gunnarbeutner/doorbell/captures/runs/our-ring-no-door/notes.md

# our-ring-no-door — our ring, session held ~59 s, then released without a door-open

Our front-door ring: line 4 goes hot, the 3-Klang gong rides the front, and a session holds for
**~58.5 s** — then it ends in a **plain release, not a door-open** (P3 never moves, no P2↔P3
bridge). So "no answer" here means **nobody opened the door**: the call was picked up / line 4
latched and held, the gong played out, and the session timed out / was hung up with the opener
never fired. Consistent with the session model from `our-ring-door-open` and `our-ring-after-neighbour`
— but ending at the *handset/timeout* side, not the door-release side.

This capture is at **50 kSa/s** — double the older 25 kSa/s runs — so the onset pedestal-then-tone
sequencing resolves cleanly (20 µs/sample).

## Capture

| | |
|---|---|
| Date | 2026-06-21 13:58:09 |
| Sample rate | **50 kSa/s** (Nyquist 25 kHz; dt = 20 µs — verified from CSV Δt and the 50 kHz WAV header) |
| Duration / points | 100.0 s, 4,999,999 samples/channel |
| Probe ratio | 10× |
| Channels (grounds on **P1**) | **CH1 = IN_P4 (= P4, bridged)**, **CH2 = P2**, **CH3 = P3** — *assumed* from the prior sessions' convention (no pre-existing note for this capture); the data is consistent with it (CH1 carries the latched line-4 pedestal + front gong, CH2 the 12 V listen line, CH3 the quiet high-Z talk line). |
| Files | `*-ch{1,2,3}.csv` / `.wav`, `*.png` |

Times are **elapsed seconds** from the start.

## Timeline

| Elapsed | Event |
|---|---|
| 0 – 31.25 s | Idle. P2 **+12.107 V**, line 4 **−0.02 V**, P3 **−0.01 V** (P3 carries ~0.59 V RMS of broadband high-Z hum, no DC). |
| **~31.250 s** | **Our ring** — line 4 (IN_P4 = P4) goes hot; pedestal rises **0.5 V → 8 V in ~5.9 ms** (1 V at 31250.0 ms, 8 V at 31255.9 ms), brief onset overshoot to ~11.1 V. P2 sags **12.1 → ~9.4 V**. **1010 Hz** gong on line 4 **and** P2. |
| 31.25 – ~35.1 s | **Gong** — 3-Klang on the front: **1010 Hz (+ strong 3030 Hz harmonic) → 840 Hz → 672 Hz**, decaying; audible for **~3.9 s**, then flat DC. |
| 31.25 – 89.79 s | **Session held — ~58.5 s.** Line 4 steady **9.25 V**, P2 **9.43 V** (line 4 sits **0.18 V below P2**, pulled up *from* P2 through the latched contact — the handset seal-in). P3 flat at 0 V the whole time (max DC excursion 0.05 V). No further bursts. |
| **~89.794 s** | **Session released — no door-open.** Line 4 collapses **9.19 → 0 V in ~34 ms**; **P2 falls *with* it** to ~2.66 V (the tied pair dropping together, CH2 staying above CH1 the whole way down), then **P2 snaps back** — 11.5 V by +44 ms, 12.1 V by +112 ms. **P3 never moves** (≤0.05 V DC). |
| 89.9 – 100 s | Idle. P2 +12.11 V, line 4 & P3 ≈ 0 V. |

## Findings

**This is *our* ring, and it was answered — but the door was never opened.** All the *our-door*
markers are present: line 4 itself goes hot (9.25 V, not just a bleed onto P2), the gong is **on
line 4**, and a session seals in and holds. What's **missing** is the door-open. In `our-ring-door-open`
and `our-ring-after-neighbour` the session ends with **P3 jumping 0 → ~7–9 V and a P2↔P3 bridge**; here P3
stays cold (max 0.05 V) and there is **no bridge** — instead the whole tied P2/line-4 pair collapses
together and P2 recovers in ~110 ms. That is a **plain seal-in release** (hang-up / call timeout),
not a door-release transfer. The discriminator is P3: a door-open shows on P3, and **P3 is flat
through the entire 100 s**. → ring answered, opener never fired.

**The end is a release, not a door-open — confirmed on three counts:**
- **P3 never rises.** A door-open is a P2↔P3 short pulling P3 up to ~7 V; here P3's DC never leaves
  the noise floor (≤0.05 V).
- **P2 is *driven* low — the TV20/S pulls P2, not line 4.** The tied pair drops together (CH2 stays
  ~0.18 V above CH1 through the fall), but the tell is *after* separation: **P2 holds a ~2.8 V plateau
  for ~18 ms while line 4 is already down near 0**, then snaps back to 12 V (~112 ms total). A *held*
  low = P2 actively driven — were line 4 the driven node, P2 would recover the instant K5 releases; P2
  also **leads** line 4 at the fall onset by ~60–100 µs. So the latch drops via a **brief P2-low
  pulse** (the K5 coil loses its P2 supply), not a P2↔P3 door-open short (slow ~1.5 s ramp,
  `door-open-standalone`).
- **No bridge meet-point.** P2 and P3 never converge to a common ~7 V level.

**Tone lags the line-4 pedestal — the reactive-suppress window is here too.** At 50 kSa/s the
onset resolves: the line-4 **pedestal** crosses 1 V at **31250.0 ms** and 8 V at **31255.9 ms**;
an **edge transient** rides the step at ~31249–31251 ms, then the AC envelope **falls back to the
noise floor** (~0.06 V) for ~31251–31262 ms before the **gong tone proper ramps in at ~31263–31265
ms** and holds. So the audible chime starts **~13–15 ms after** the pedestal begins — the same
~10–15 ms gap noted in `our-ring-after-neighbour`. Enough to suppress the gong **reactively** (a relay's ~5 ms
pull-in just fits; a PhotoMOS fits easily) — chime-suppress does **not** need pre-arming.

**Gong:** **~1010 Hz** fundamental with a strong **3030 Hz** 3rd harmonic at onset, descending
through **~840 Hz** to **~672 Hz** (the 3-Klang, a falling sequence), decaying over ~3.9 s — matches
the 1010 / 3032 / 672 Hz chime of `our-ring-door-open` and `neighbour-ring-door-open`.

Fitted additive model (heterodyne envelope tracking + Theil–Sen exponential fit on the
bandpassed/denoised CH1 audio; onset amplitudes in dB re the strike-1 peak-normalised extract):
the fundamentals sit at **6:5:4 over the 672 Hz root — a descending major triad** (fifth, third,
root), and each strike is an **odd-harmonic series** (1f, 3f, 5f, 7f…) — the signature of the
TV20/S tone generator, not a struck bell.

| Strike (onset) | Partials — f (Hz) / onset dB / τ (ms) |
|---|---|
| 1 (0 ms) | 1010.2 / −5.8 / 1353 · 3030.7 / −17.9 / 1361 · 5051.1 / −27.8 / 1439 |
| 2 (790 ms) | 840.5 / −9.2 / 1135 · 2521.6 / −21.3 / 1332 · 4202.7 / −29.2 / 1468 · 5883.8 / −38.8 / 1740 · 1849.2 / −42.5 / 4093 |
| 3 (1552 ms) | 672.4 / −10.8 / 1502 · 2017.2 / −20.8 / 1480 · 3362.0 / −27.3 / 1414 · 4706.8 / −33.6 / 1452 · 6051.6 / −40.9 / 1889 |

The 1010 Hz fundamental beats (a close doublet — its envelope has periodic nulls), so short-window
decay fits fail on it; the τ values above come from full-ring-out tracking with noise-floor
truncation. `firmware/sounds/candidates/gong-remaster.wav` is a noise-free additive resynthesis
from this table.

**Session geometry matches the handset seal-in model.** Line 4 holds at **9.25 V**, **0.18 V below
P2 (9.43 V)** — line 4 is pulled up *from* P2 through the latched contact, not driven by the
TV20/S, so it tracks just under P2 (the same 0.1–0.2 V offset as the other held sessions). P2's
~2.67 V sag (12.11 → 9.43 V) is the latched coil loading the shared line. The session simply runs
its course (~58.5 s) and releases — no door in the loop.

## Notes

- **IN_P4↔P4 bonded** for this run, so CH1 is line 4 itself (WF26 coil + C1 in the loop); a
  "line 4 hot" reading is unambiguously *our* door.
- **P3 (CH3) idles as a high-Z antenna** — ~0.59 V RMS, ~4.7 Vpp, **broadband (strongest 0.6–3.5
  kHz), DC-free** — same high-impedance-node signature as IN_P4 in `neighbour-ring-door-open`. It
  carries no DC at any point, which is exactly why "P3 never moves" is a clean no-door-open test.
- The ~58.5 s hold is much longer than the ~10–13 s sessions that ended in a door-open
  (`our-ring-door-open`, `our-ring-after-neighbour`) — consistent with a call left to time out / hang up rather than
  cut short by the opener.

Related: `our-ring-door-open` (own ring + door-open, the clean session model),
`our-ring-after-neighbour` (own ring + door-open, with a neighbour ring first),
`door-open-standalone` (standalone ÖT — what a real door-open looks like on the bus, absent
here). Bus model: `../DESIGN.md` ("Bell signals", "Door opener", "WF26 internal circuit").
