gunnarbeutner/doorbell/captures/runs/door-open-standalone/notes.md

# door-open-standalone — our own door-opener, triggered standalone

A scope capture of **our** door-opener (ÖT) fired on its own, with **no ring/call active**, to see
the trigger waveform on the bus in isolation. Grabbed with `capture.py --screen` (the displayed
ROLL window, full sample density) — see the scope screenshot `door-open-standalone.jpeg`.

## Capture

| | |
|---|---|
| Date | 2026-06-17 16:57:05 |
| Mode | `--screen` (on-screen window, ROLL) |
| Sample rate | 25 kSa/s |
| Duration / points | 8.00 s, 200,000 samples/channel |
| Probe ratio | 10× |
| Channels (grounds on **P1**) | **CH1 = IN_P4**, **CH2 = P2**, **CH3 = P3** |
| Files | `*-ch{1,2,3}.csv` / `.wav`, `*.png` (DC+AC overview), `door-open-standalone.jpeg` (scope screen) |

Times are **elapsed seconds** from the start (scope axis runs −8.0…0.0 s, trigger at −3 s = 5.0 s
elapsed).

## Timeline

| Elapsed | Event |
|---|---|
| 0 – 1.75 s | Idle. P2 +12.06 V, P3 +0.04 V, IN_P4 ≈ 0 V. |
| **~1.75 s** | **Door-opener engages** — P2↔P3 short. P2 drops fast (12 → ~7 V), P3 snaps up (0 → ~7 V). |
| 2.0 – 3.4 s | **Bridged: both held at ~7.16 V** (P2 7.14, P3 7.18 — essentially equal) for ~1.5 s. |
| **~3.5 s** | **Released** — P3 snaps back to 0 V quickly; **P2 recovers slowly**, ramping 7 → 12 V over ~1.5 s (τ ≈ 0.5 s, with a stall near 10 V). |
| 5.25 – 8 s | Idle again. |

## What it shows / confirms

- **Pure P2↔P3 operation — line 4 untouched.** IN_P4 stays flat at ~0 V (±0.4 V noise floor) the
  whole time, with **no coupling even at the switching edges**. The door-opener is exactly the
  TV20/S test *"Klemmen 2 u. 3 brücken,"* nothing on line 4 — validating **K2 = a direct P2↔P3
  short**.
- **It's a dead short, not a resistive bridge.** P2 and P3 are forced to the *same* level
  (7.14 vs 7.18 V). A 2.2 kΩ bridge (the talk handshake) would leave them *separated*; equal means
  a true short. So the door path is cleanly distinguished from the talk path — the practical side of
  the "short fires the opener, 2.2 kΩ doesn't" threshold.
- **The meet point (~7.16 V) is impedance-divided, not midpoint.** From 12 V and 0 V landing at
  7.16 V ⇒ P2's source is ~1.5× stiffer than P3's pull-to-0 (R3/R2 ≈ 1.5).
- **Asymmetric recovery (new):** the short yanks P2 *down* fast (low-Z), but P2 climbs *back* slowly
  (~1.5 s, τ ≈ 0.5 s) through its own bias-source resistance into the bus capacitance. So **after a
  door-open, line 2 takes ~1.5 s to settle back to 12 V** — the codec's RX tap would see a slow DC
  drift upward for ~1.5 s following any door-open (relevant to RX timing / AGC).
- **No audio.** Standalone open (no ring) ⇒ pure DC bridge + switching transients at the make/break
  edges; nothing tonal.

## Caveat

This is the **trigger waveform** as seen on our bus, **not** the opener *firing*. The actual
8–12 V AC solenoid current is switched at the TV20/S / door end, off our tap — to confirm the door
physically released you'd need to hear/see it (or scope the opener pair).

Related: `neighbour-ring-door-open` (neighbour ring with a door-open mid-call),
`neighbour-ring-5ksps`, `idle-20260617-143740`. Bus model: `../DESIGN.md` ("Door opener",
"WF26 internal circuit").
