gunnarbeutner/doorbell/docs/design/HJR4102.PDF

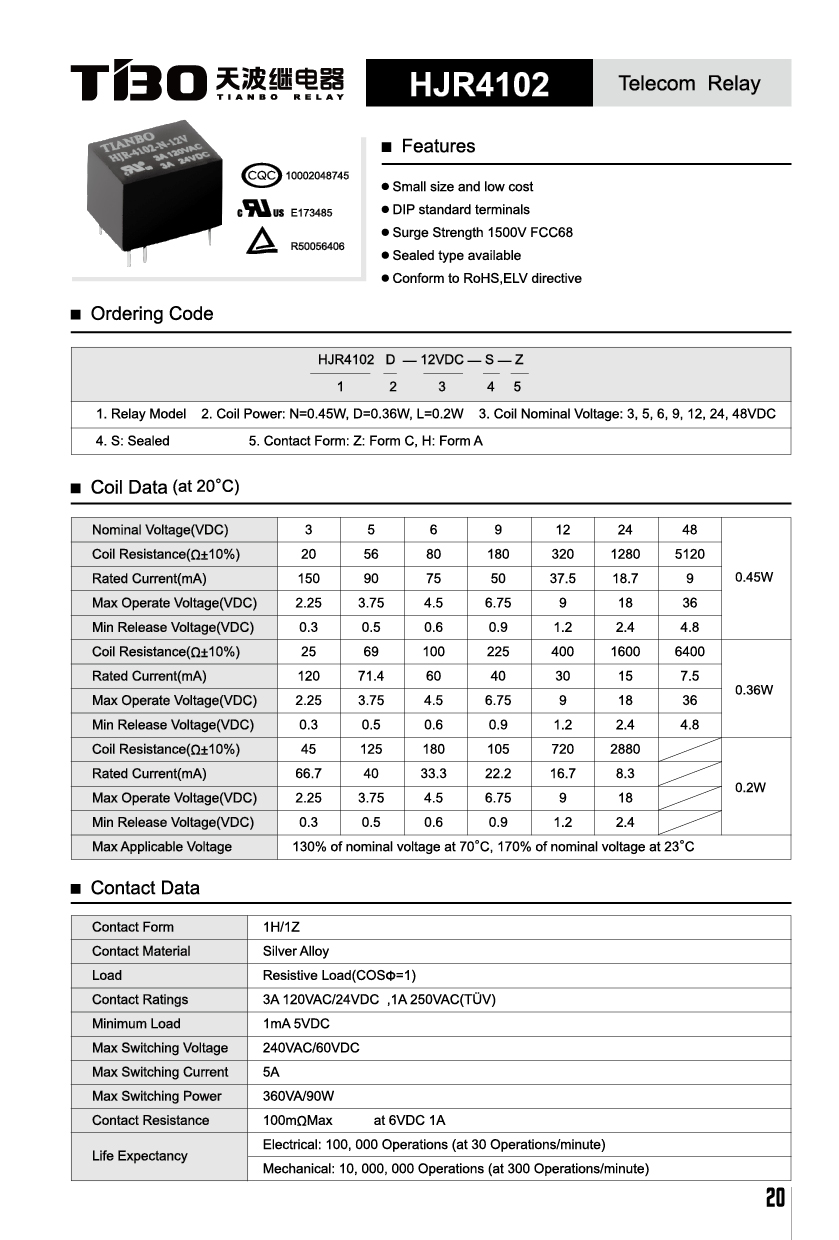
[picture p2: page 1]
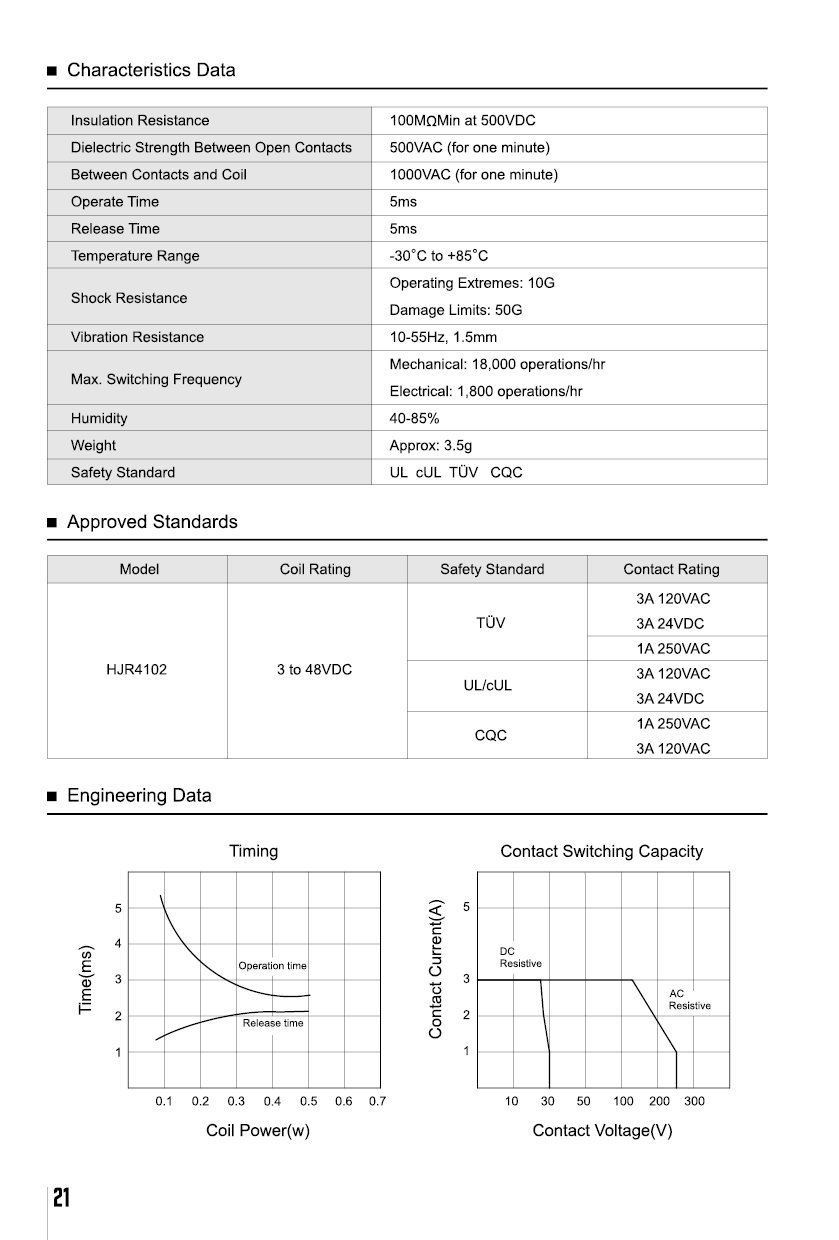
[picture p3: page 2]
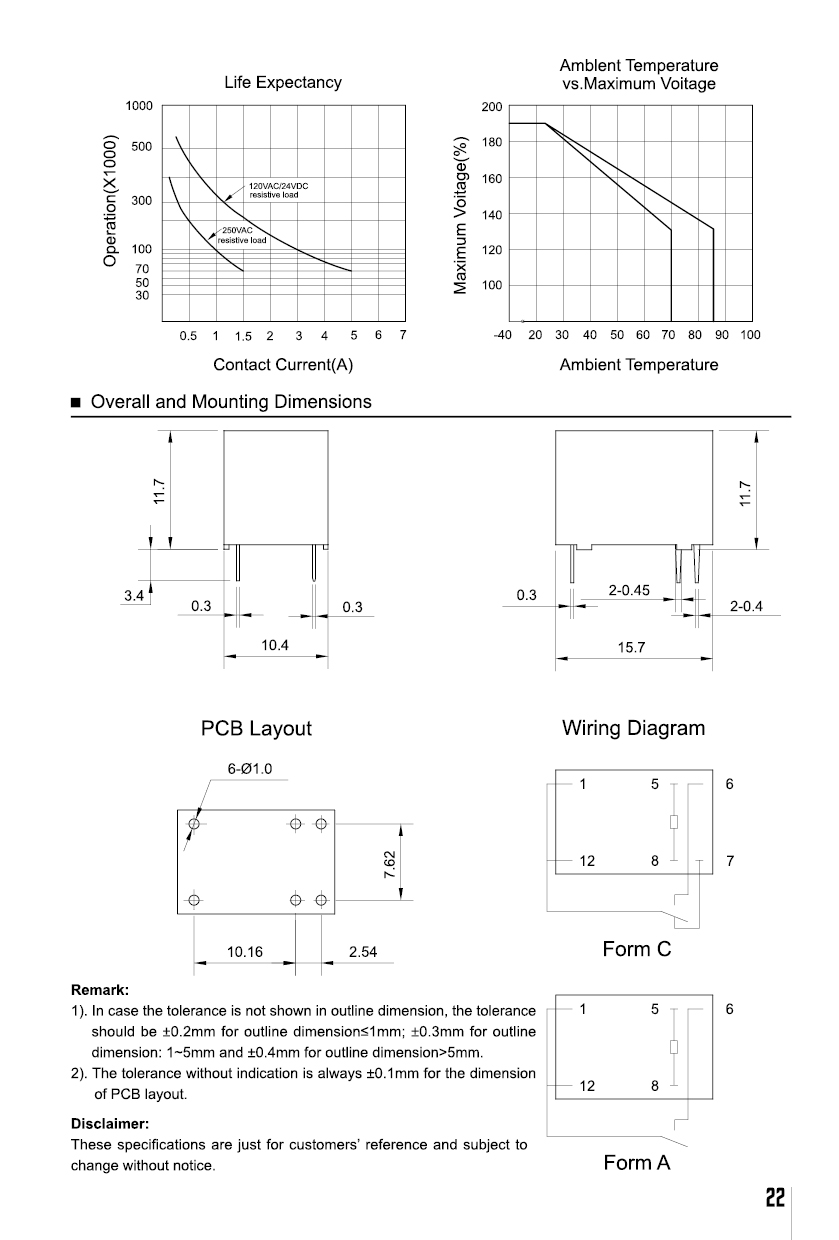
[picture p4: page 3]
