gunnarbeutner/doorbell/captures/runs/door-open-call-held/preview.png

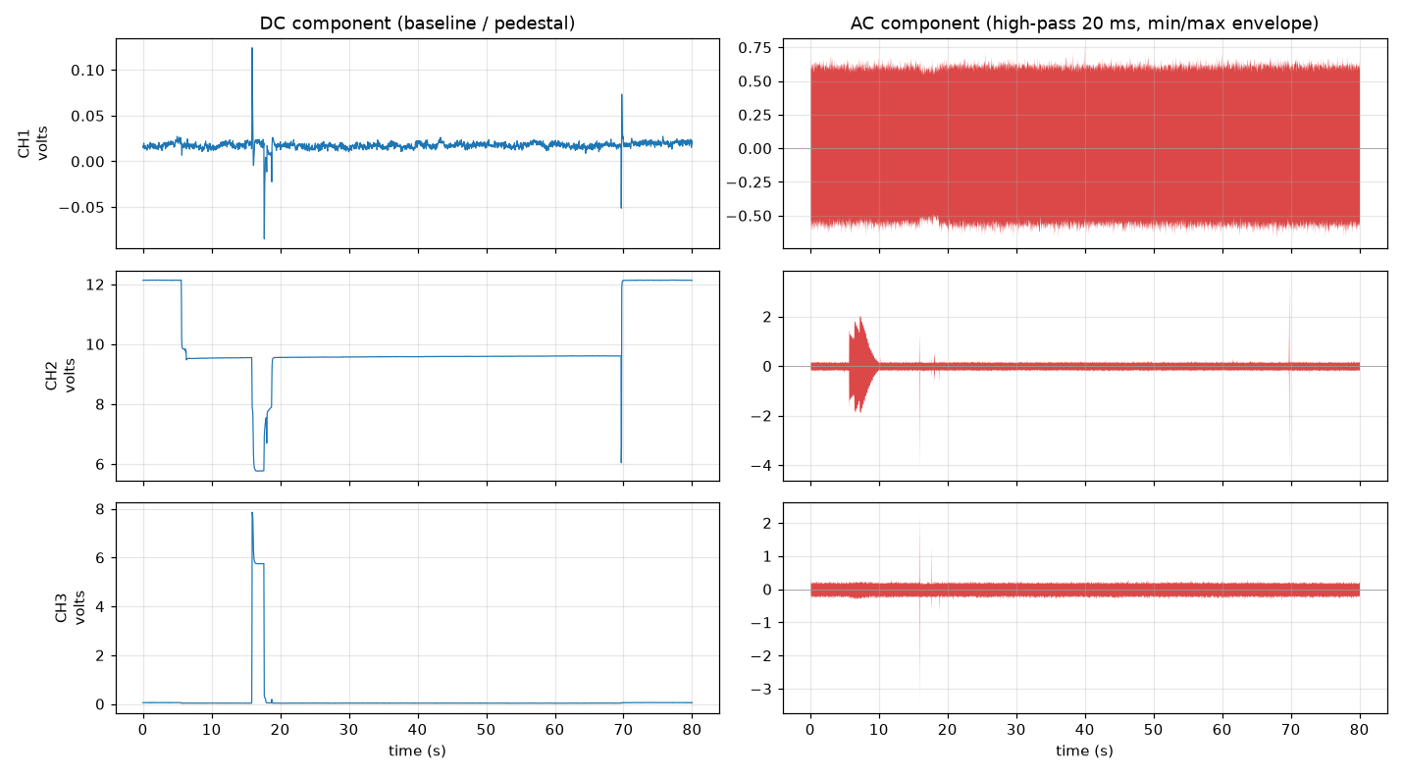
captures/runs/door-open-call-held/preview.png
