gunnarbeutner/doorbell/captures/runs/door-open-standalone/preview.jpeg

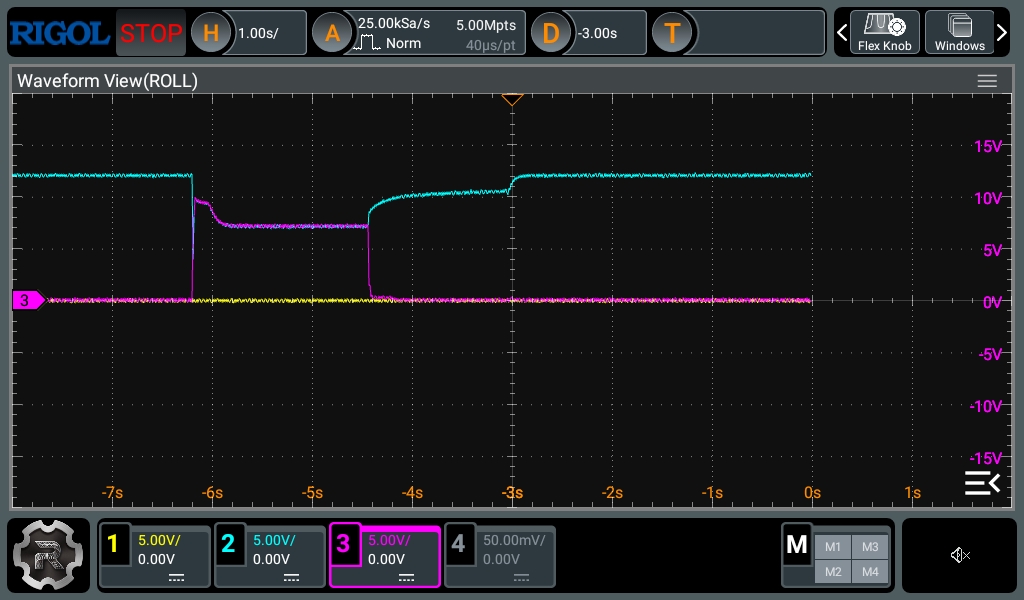
captures/runs/door-open-standalone/preview.jpeg
