gunnarbeutner/doorbell/captures/runs/door-open-standalone/preview.png

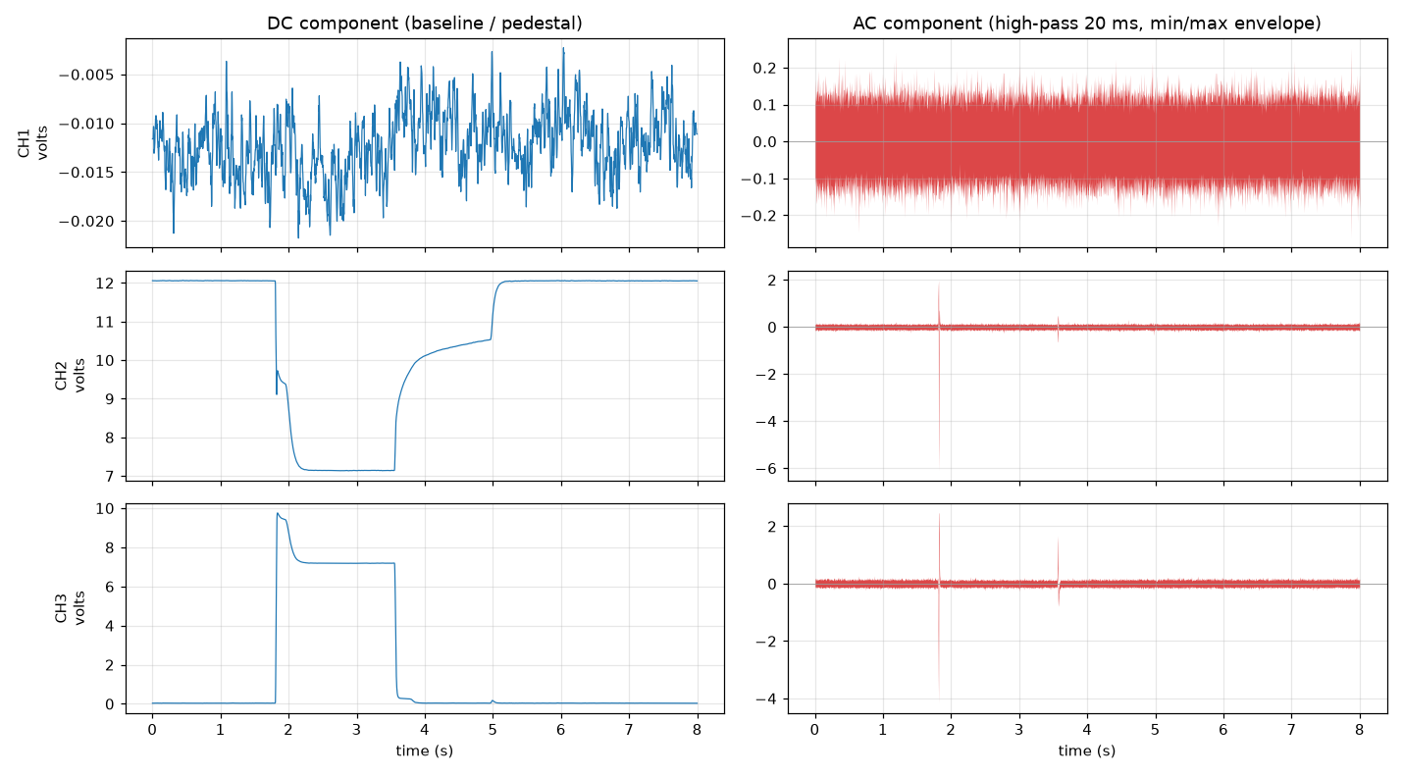
captures/runs/door-open-standalone/preview.png
