gunnarbeutner/doorbell/captures/runs/floor-call-p5/preview.png

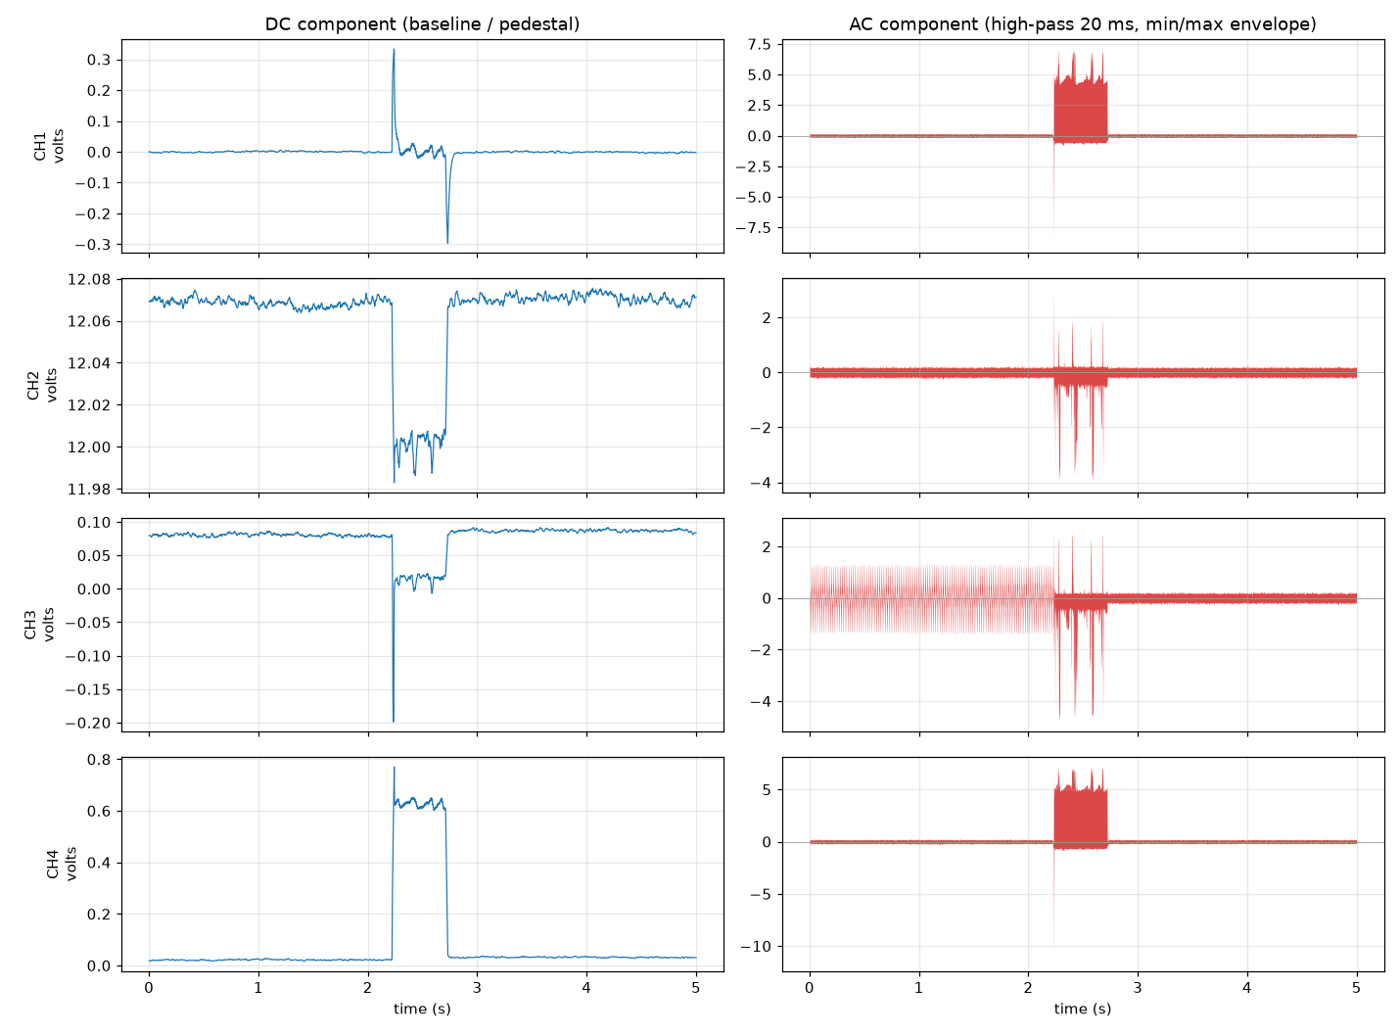
captures/runs/floor-call-p5/preview.png
