gunnarbeutner/doorbell/captures/runs/neighbour-ring-5ksps/preview.png

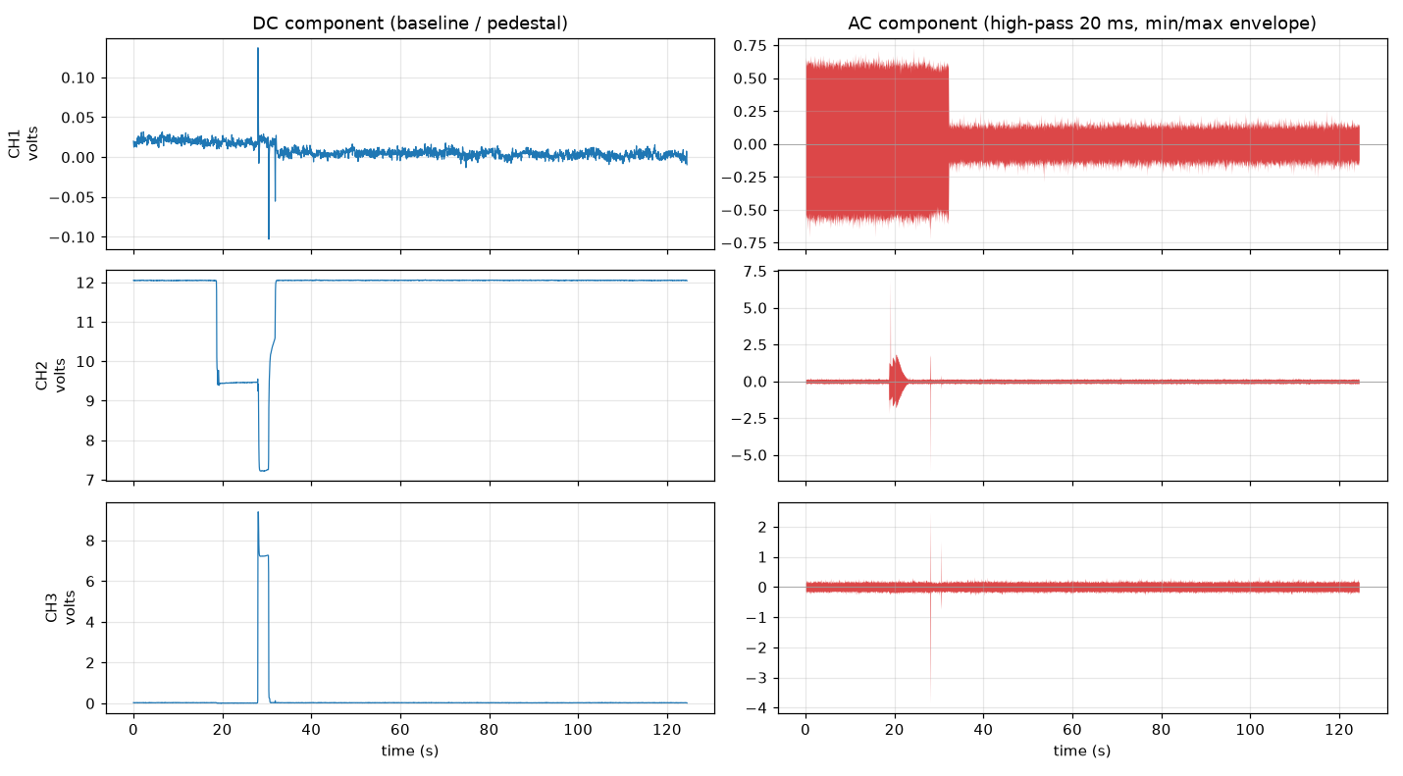
captures/runs/neighbour-ring-5ksps/preview.png
