gunnarbeutner/doorbell/captures/runs/neighbour-ring-door-open/preview.png

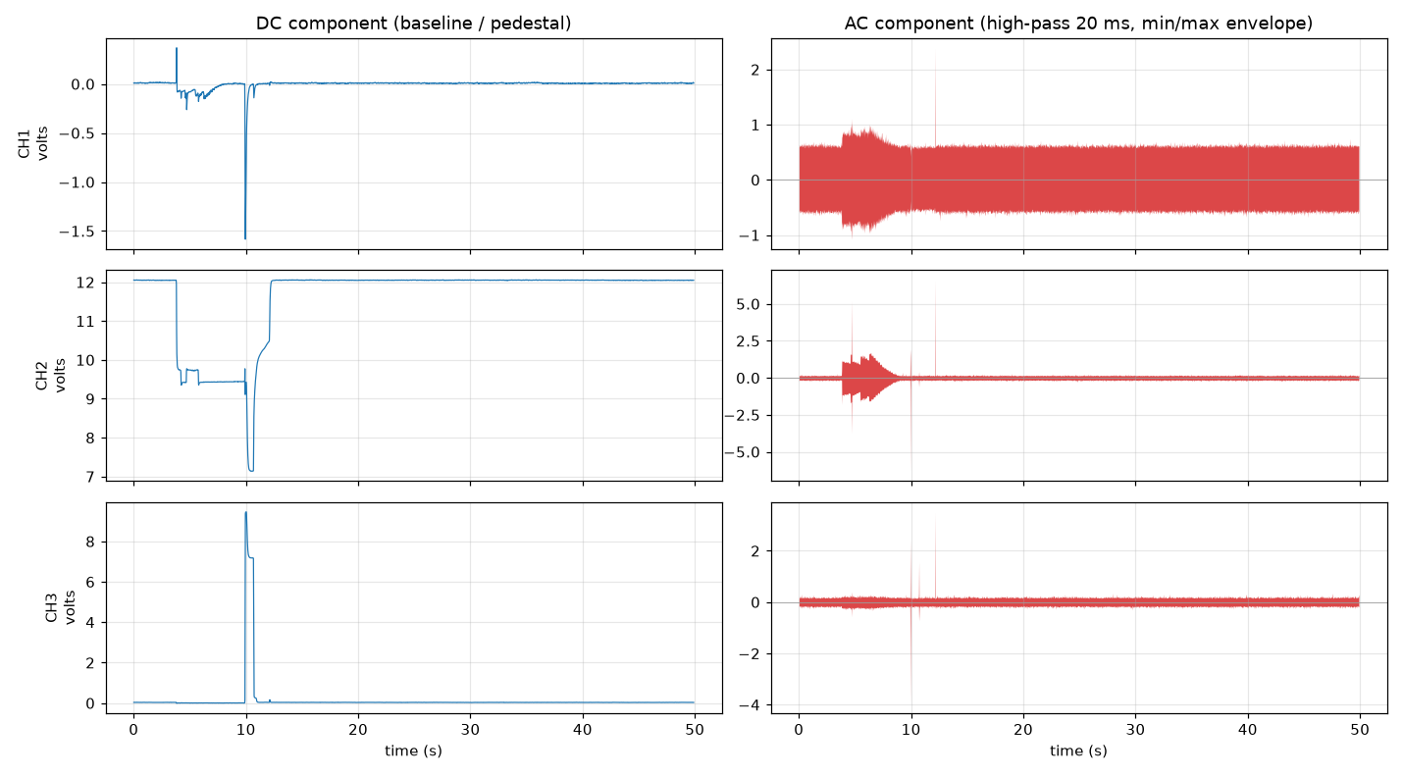
captures/runs/neighbour-ring-door-open/preview.png
