gunnarbeutner/doorbell/captures/runs/our-ring-after-neighbour/preview.png

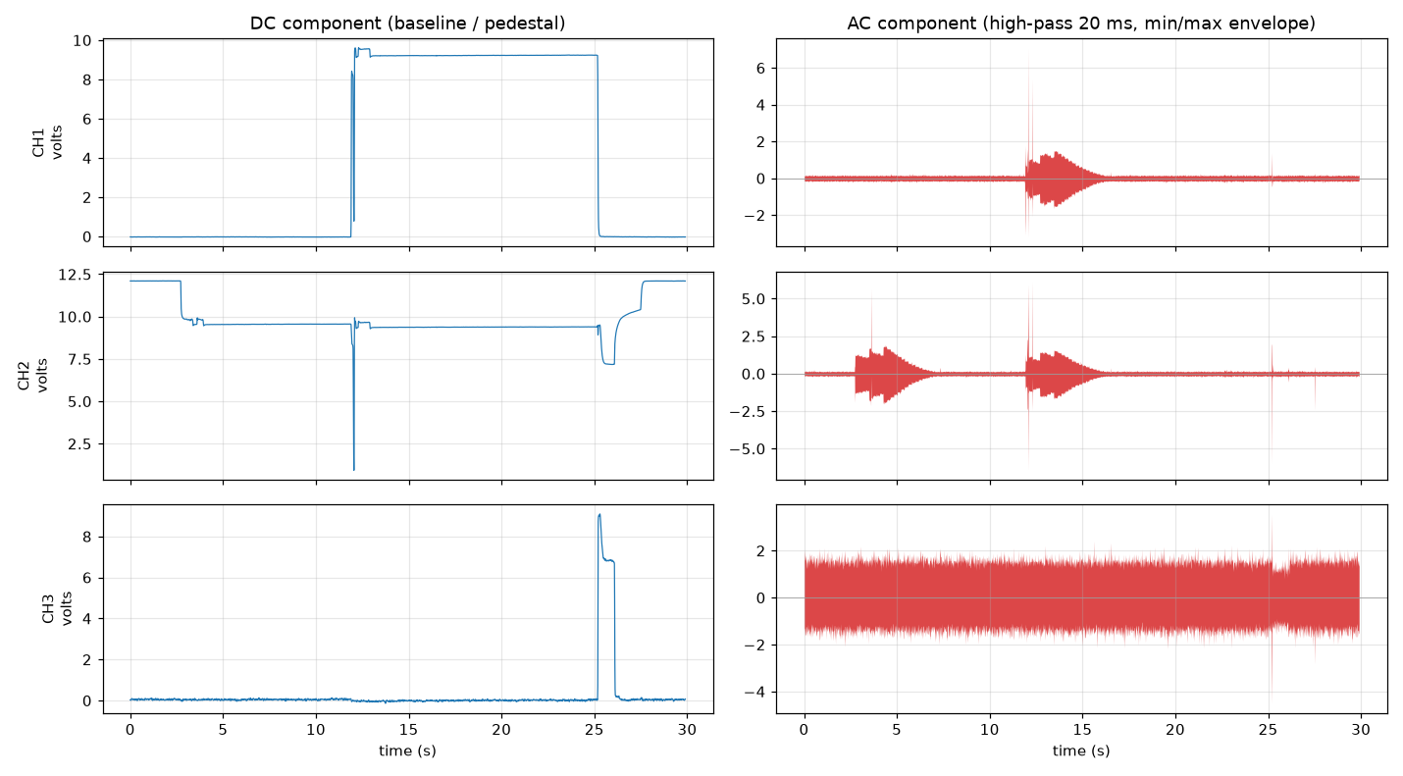
captures/runs/our-ring-after-neighbour/preview.png
