gunnarbeutner/doorbell/captures/runs/our-ring-door-open/preview.png

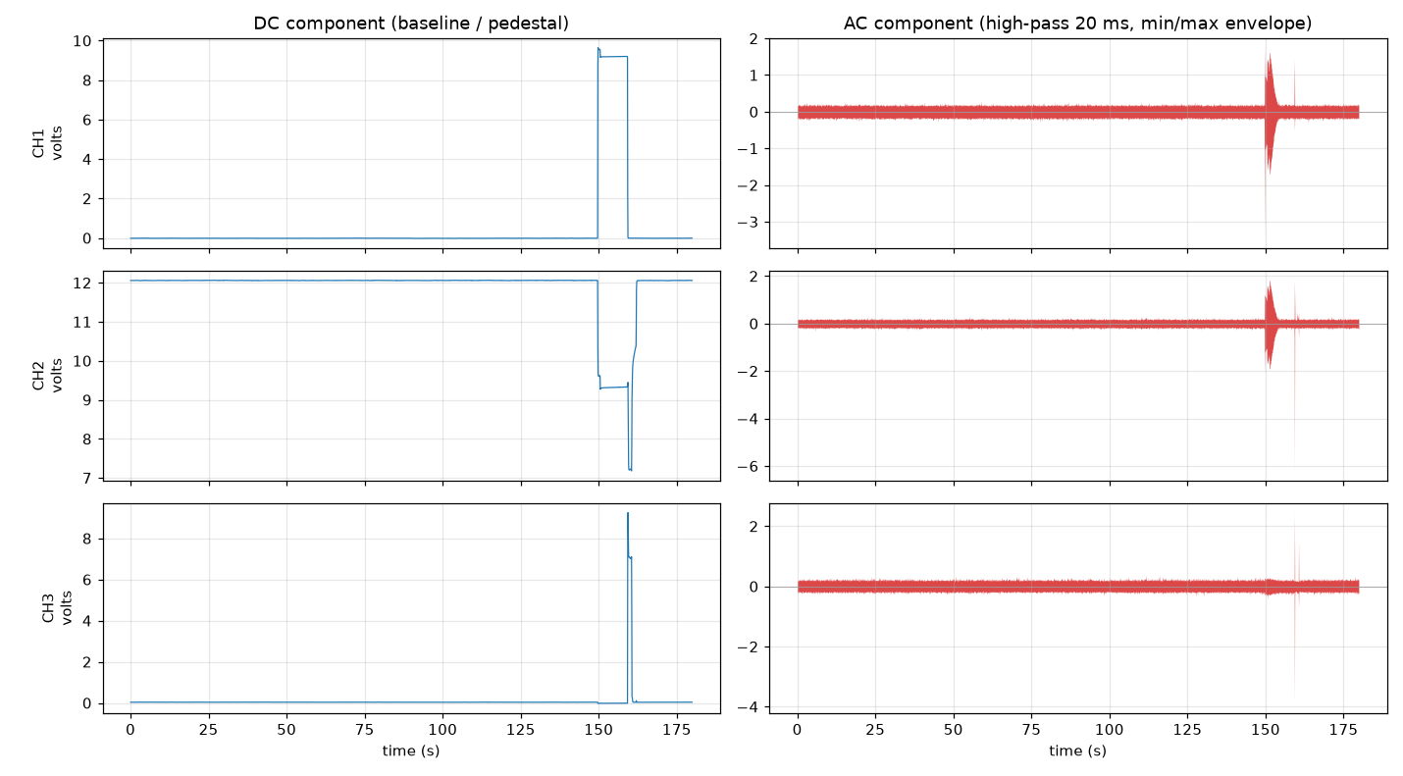
captures/runs/our-ring-door-open/preview.png
