gunnarbeutner/doorbell/captures/runs/our-ring-no-door/preview.png

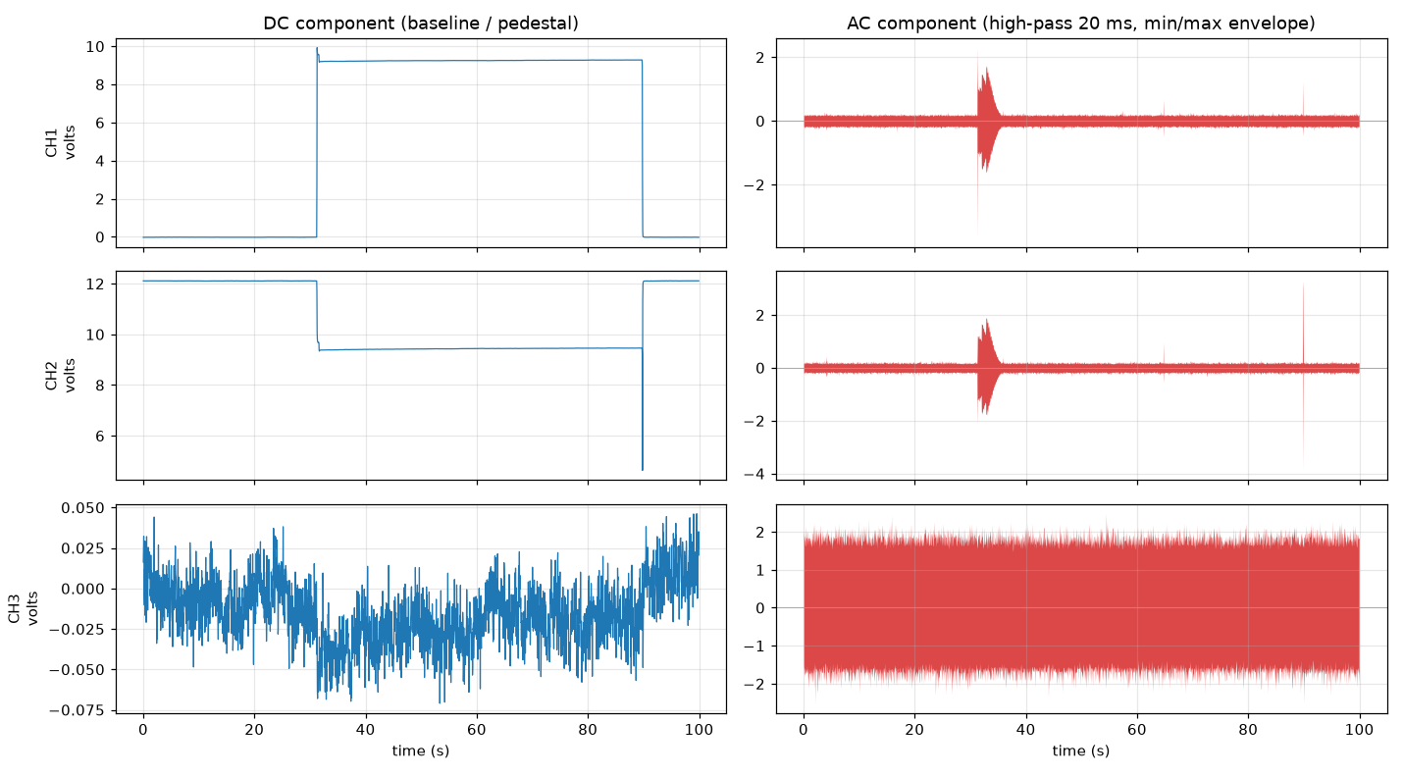
captures/runs/our-ring-no-door/preview.png
