gunnarbeutner/doorbell/captures/runs/our-ring-p4-floating/p1-p4-ring.png

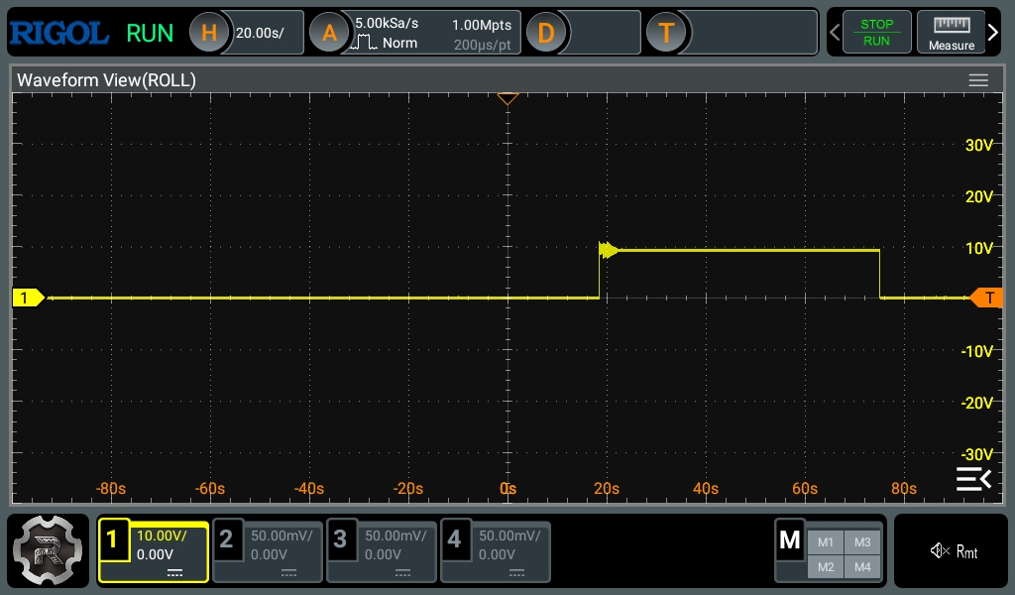
captures/runs/our-ring-p4-floating/p1-p4-ring.png
