gunnarbeutner/doorbell/captures/runs/our-ring-p4-floating/preview.png

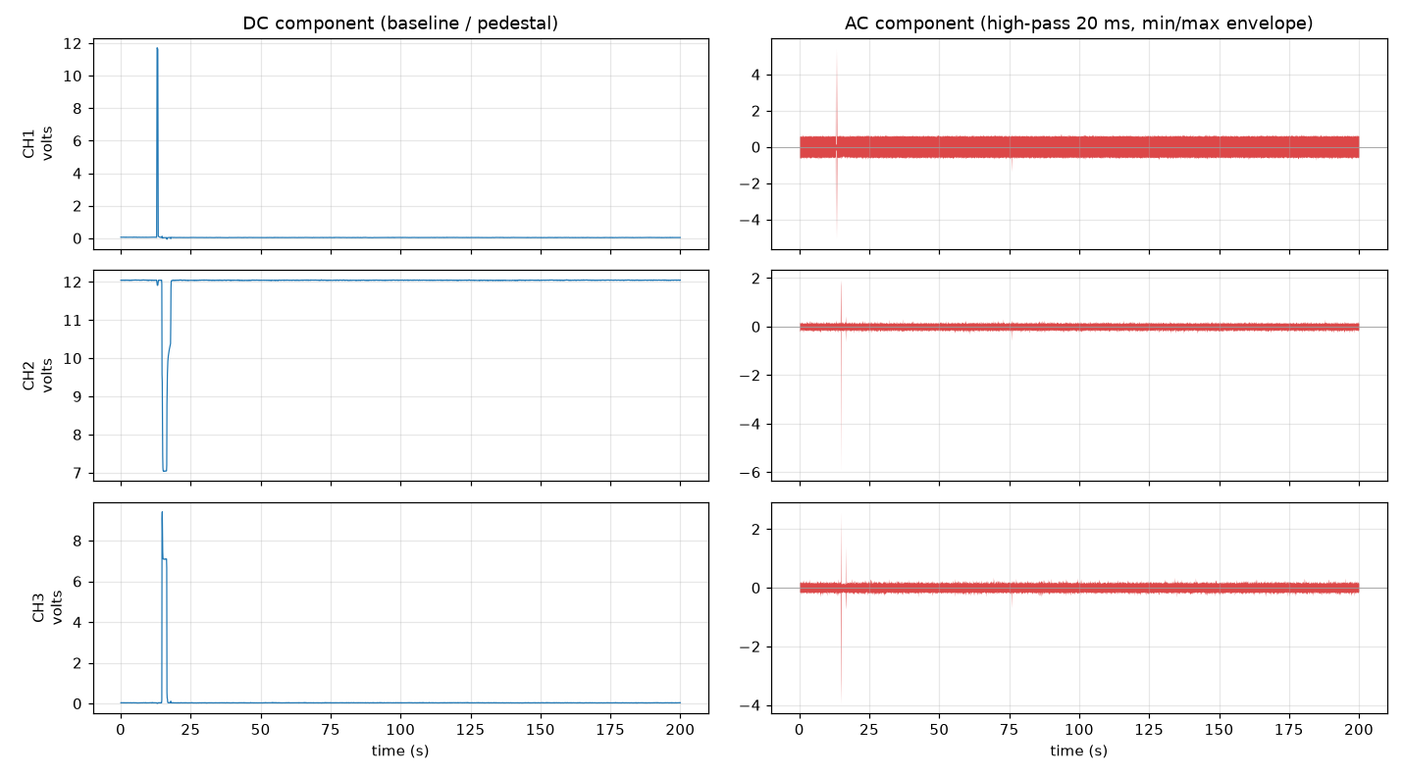
captures/runs/our-ring-p4-floating/preview.png
