gunnarbeutner/doorbell/docs/scope/k3-usb-power-loss.png

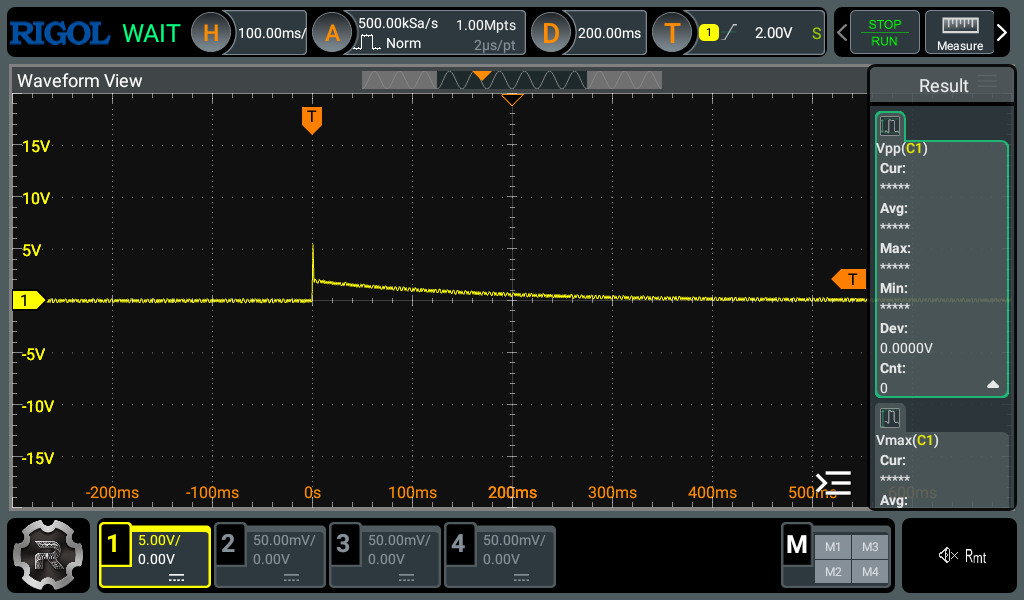
docs/scope/k3-usb-power-loss.png
