gunnarbeutner/doorbell/docs/scope/welcome-chime-p3.png

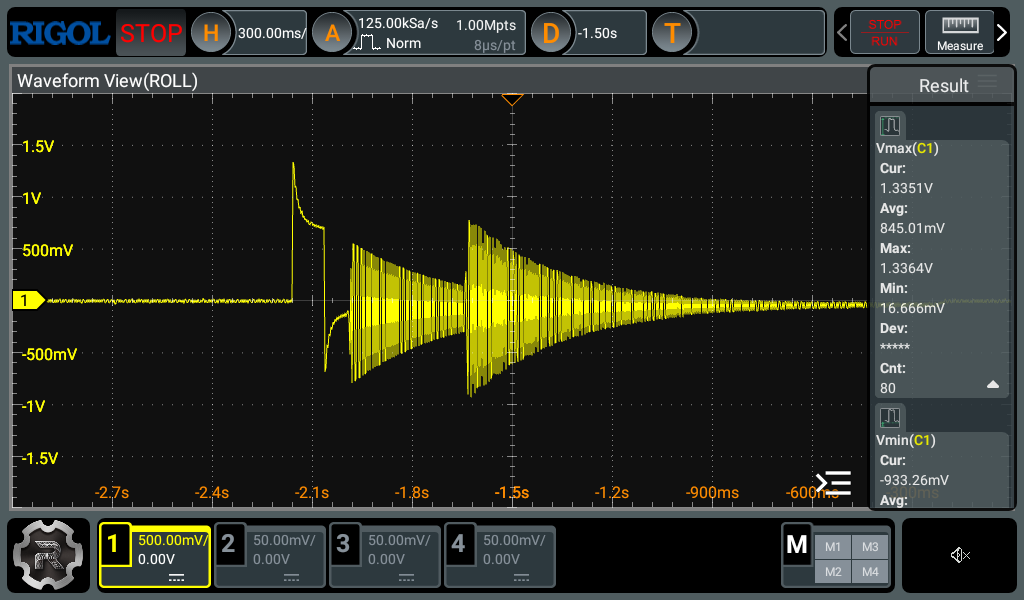
docs/scope/welcome-chime-p3.png
