gunnarbeutner/doorbell/docs/scope/door-break-before-make.png

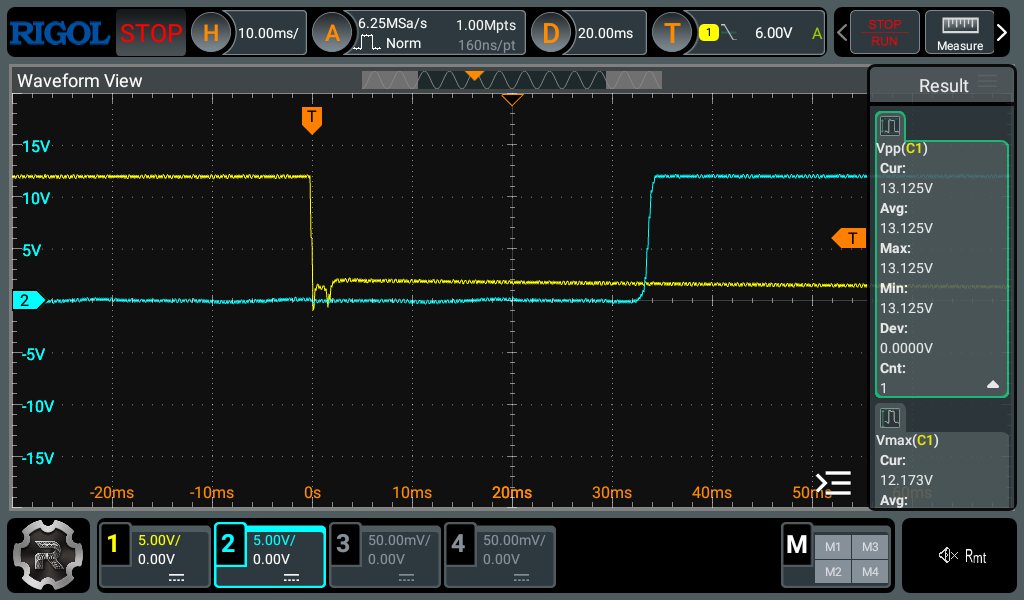
docs/scope/door-break-before-make.png
