gunnarbeutner/doorbell/sim/firmware-test/circuit-runner.js

import { EventEmitter } from 'node:events';
import net from 'node:net';

import { importNetlist } from '../src/import.js';
import { buildElements, defaultSwitchState } from '../src/components/index.js';
import { createStepper, gndOf, makeWave } from '../src/engine.js';
import { Tv20sEnvironment } from '../src/tv20s/environment.js';

export const PROTOCOL_VERSION = 1;

const GPIO_TO_SIGNAL = Object.freeze({
  4: 'K5_SENSE_N',
  5: 'VBUS_F_ADC',
  9: 'PTT_DRV',
  10: 'DOOR_DRV',
  11: 'MUTE_DRV',
  12: 'P4_SENSE_N',
  13: 'P5_SENSE_N',
  47: 'PTT_SENSE_N',
  48: 'P4_ISO',
});

const EXPECTED_U1 = Object.freeze({
  4: '/K5_SENSE_N',
  5: '/VBUS_F_ADC',
  17: '/PTT_DRV',
  18: '/DOOR_DRV',
  19: '/MUTE_DRV',
  20: '/P4_SENSE_N',
  21: '/P5_SENSE_N',
  24: '/PTT_SENSE_N',
  25: '/P4_ISO',
});

const IMPORTANT_NETS = ['/P2', '/P3', '/P4', '/P5', '/K5_LATCH', '/K6_RET', '/CHIME_POS'];

let cachedHeadNetlist;
let cachedReferenceNetlist;
const cachedDefaultStates = new Map();

function liveHeadNetlist() {
  // Every suite invocation imports HEAD from KiCad. Reusing the immutable result within that
  // invocation avoids launching kicad-cli once per fresh firmware scenario.
  cachedHeadNetlist ??= importNetlist();
  return cachedHeadNetlist;
}

function liveReferenceNetlist() {
  cachedReferenceNetlist ??= importNetlist('wf26');
  return cachedReferenceNetlist;
}

function source(value = 0) {
  if (value === null) return { kind: 'off', value: 0, offset: 0, amplitude: 0, frequency: 0 };
  return { kind: 'dc', value, offset: 0, amplitude: 0, frequency: 0 };
}

export class HeadCircuitFixture {
  constructor({ startMs = 0, timeline = [], netlist, onSample = null, environment = 'lab',
    referenceNetlist } = {}) {
    this.netlist = netlist || liveHeadNetlist();
    this.validateHeadMapping();
    this.timeline = timeline;
    this.startMs = Number(startMs);
    this.nowMs = Number(startMs);
    this.electricalMs = Number(startMs);
    this.electricalSeconds = 0;
    this.fineUntilMs = this.nowMs;
    this.mediumUntilMs = this.nowMs;
    this.externalToneActive = false;
    this.outputs = { PTT_DRV: false, DOOR_DRV: false, MUTE_DRV: false, P4_ISO: false };
    this.mediaActive = false;
    this.sources = {
      P2: source(12),
      P4: source(null),
      P5: source(null),
      VBUS: source(5),
    };
    this.switches = { ...defaultSwitchState(this.netlist), SW3: false, SW4: false };
    this.programPresent = true;
    this.lastInputMask = null;
    this.indeterminateSince = {};
    this.lastElectrical = {};
    this.onSample = onSample;
    if (!['lab', 'tv20s'].includes(environment)) throw new Error(`unknown circuit environment ${environment}`);
    this.environmentMode = environment;
    this.tv20s = environment === 'tv20s' ? new Tv20sEnvironment({
      startMs, calibration: undefined, referenceNetlist: referenceNetlist || liveReferenceNetlist(),
      ground: gndOf(this.netlist),
    }) : null;
    this.interactiveSources = null;
    this.interactiveExtra = [];
    this.dcOperatingPoint = null;
    const cacheKey = `${environment}:${this.netlist.source}`;
    const cachedDefaultState = cachedDefaultStates.get(cacheKey);
    this.rebuild(0.0002, cachedDefaultState);
    if (cachedDefaultState === undefined) {
      // Fixture initialization represents a board whose standing rails have already reached their
      // DC operating point. Solve that point directly; do not confuse an arbitrary transient duration
      // with electrical settling. Every scenario receives its own copy of this immutable seed.
      const settled = this.stepper.operatingPoint(this.electricalSeconds).state;
      cachedDefaultStates.set(cacheKey, settled);
      this.rebuild(0.0002, settled);
    }
    this.fineUntilMs = this.nowMs;
    this.mediumUntilMs = this.nowMs;
    this.timeline.length = 0;
    this.lastElectrical = {};
    this.recordElectrical(true);
    this.lastInputMask = this.readInputs().mask;
    this.recordSample();
  }

  validateHeadMapping() {
    const u1 = this.netlist.components.find((component) => component.ref === 'U1');
    if (!u1) throw new Error('HEAD mapping: U1 is missing');
    for (const [pin, expected] of Object.entries(EXPECTED_U1)) {
      if (u1.pins[pin] !== expected)
        throw new Error(`HEAD mapping: U1 pin ${pin} must be ${expected}, got ${u1.pins[pin] ?? '(missing)'}`);
    }
    const j2 = this.netlist.components.find((component) => component.ref === 'J2');
    const expectedBus = { 1: 'GND', 2: '/P2', 3: '/P3', 4: '/P4', 5: '/P5' };
    for (const [pin, expected] of Object.entries(expectedBus))
      if (j2?.pins[pin] !== expected)
        throw new Error(`HEAD mapping: J2.${pin} must be ${expected}, got ${j2?.pins[pin] ?? '(missing)'}`);
  }

  validateHello(tokens) {
    const advertised = Object.fromEntries(tokens.map((token) => token.split('=')));
    for (const [pin, signal] of Object.entries(GPIO_TO_SIGNAL)) {
      if (advertised[signal] !== pin)
        throw new Error(`HELLO mapping mismatch for ${signal}: expected GPIO${pin}, got ${advertised[signal] ?? 'missing'}`);
    }
  }

  valueAt(name) {
    const spec = this.sources[name];
    if (spec.kind === 'tone')
      return spec.offset + spec.amplitude * Math.sin(2 * Math.PI * spec.frequency * this.electricalSeconds);
    if (spec.kind === 'pulse') {
      const elapsedMs = (this.electricalSeconds - spec.startedSeconds) * 1000;
      if (elapsedMs < spec.delayMs) return spec.low;
      const activeMs = elapsedMs - spec.delayMs;
      if (spec.count !== null && activeMs >= spec.count * spec.periodMs) return spec.low;
      return activeMs % spec.periodMs < spec.widthMs ? spec.high : spec.low;
    }
    if (spec.kind === 'captured') {
      const elapsedMs = Math.max(0, (this.electricalSeconds - spec.startedSeconds) * 1000);
      const last = spec.values.length - 1;
      const position = Math.min(last, elapsedMs / spec.dtMs);
      const index = Math.floor(position);
      const fraction = position - index;
      return spec.values[index] + fraction * ((spec.values[index + 1] ?? spec.values[index]) - spec.values[index]);
    }
    return spec.value;
  }

  refreshExternalWave() {
    const waves = Object.values(this.sources).filter((item) =>
      item.kind === 'tone' || item.kind === 'pulse' || item.kind === 'captured');
    this.externalToneActive = waves.length !== 0;
    this.externalStepSeconds = Math.min(0.00025, ...waves.map((item) => {
      if (item.kind === 'captured') return item.dtMs / 1000;
      if (item.kind === 'pulse')
        return Math.max(0.00002, Math.min(item.widthMs, item.periodMs - item.widthMs) / 4000);
      return 1 / (item.frequency * 6);
    }));
  }

  program() {
    if (!this.programPresent) return {};
    return {
      U1: {
        '/PTT_DRV': () => (this.outputs.PTT_DRV ? 3.3 : 0),
        '/DOOR_DRV': () => (this.outputs.DOOR_DRV ? 3.3 : 0),
        '/MUTE_DRV': () => (this.outputs.MUTE_DRV ? 3.3 : 0),
        '/P4_ISO': () => (this.outputs.P4_ISO ? 3.3 : 0),
      },
      U3: {
        out: {
          // A bounded, non-harmonic-to-the-1 ms-step codec representative. It is not a TV20/S
          // acoustic model; it only exercises the board's TX coupling while firmware owns media.
          p: () => 1.65 + (this.mediaActive ? 0.35 * Math.sin(2 * Math.PI * 333 * this.electricalSeconds) : 0),
          n: () => 1.65,
        },
      },
    };
  }

  rebuild(dt, seed = this.stepper?.extractState()) {
    this.dt = dt;
    if (this.tv20s) {
      this.tv20s.syncTime(this.electricalMs);
      const elements = buildElements(this.netlist, {
        switchState: this.switches,
        program: this.program(),
        extra: this.tv20s.extraElements(),
      });
      const sources = [
        { net: '/VBUS', vf: () => this.valueAt('VBUS') },
        ...this.tv20s.sources(),
      ];
      this.stepper = createStepper(elements, sources, gndOf(this.netlist), dt, seed);
      return;
    }
    if (this.interactiveSources !== null) {
      const extra = [...this.interactiveExtra];
      const sources = [];
      for (let index = 0; index < this.interactiveSources.length; index++) {
        const item = this.interactiveSources[index];
        if (item.off) continue;
        const wave = makeWave(item);
        const impedance = Number(item.impedance || 0);
        if (impedance > 0) {
          const sourceNet = `/INTERACTIVE_SOURCE_${index}`;
          extra.push({ type: 'R', a: sourceNet, b: item.net, value: impedance,
            ref: `INTERACTIVE_SOURCE_R${index}` });
          sources.push({ net: sourceNet, vf: () => wave(this.electricalSeconds) });
        } else {
          sources.push({ net: item.net, vf: () => wave(this.electricalSeconds) });
        }
      }
      const elements = buildElements(this.netlist, {
        switchState: this.switches,
        program: this.program(),
        extra,
      });
      this.stepper = createStepper(elements, sources, gndOf(this.netlist), dt, seed);
      return;
    }
    const connectedBusSources = ['P2', 'P4', 'P5'].filter((name) => this.sources[name].kind !== 'off');
    const extra = connectedBusSources.map((name) => ({
      type: 'R',
      a: `/TEST_${name}_SOURCE`,
      b: `/${name}`,
      value: 90,
      ref: `TEST_${name}_SOURCE_R`,
    }));
    const elements = buildElements(this.netlist, {
      switchState: this.switches,
      program: this.program(),
      extra,
    });
    const sources = [{ net: '/VBUS', vf: () => this.valueAt('VBUS') },
      ...connectedBusSources.map((name) => ({ net: `/TEST_${name}_SOURCE`, vf: () => this.valueAt(name) }))];
    this.stepper = createStepper(elements, sources, gndOf(this.netlist), dt, seed);
  }

  invalidateOperatingPoint() {
    this.dcOperatingPoint = null;
  }

  atOperatingPoint() {
    if (this.externalToneActive || this.mediaActive || this.tv20s?.hasDynamics(this.electricalMs)) return false;
    if (this.dcOperatingPoint == null) {
      try {
        this.dcOperatingPoint = this.stepper.operatingPoint(this.electricalSeconds);
      } catch (error) {
        // A hard fault can have no numerically solvable DC point in its present discrete topology
        // (for example, the intact fuse feeding the 50 V clamp test). That is not permission to skip
        // or to weaken the transient solver: keep stepping adaptively until the topology changes, then
        // retry the operating-point solve. Non-convergence of the real transient still propagates.
        if (/nonlinear solve did not converge/.test(error.message)) return false;
        throw error;
      }
    }
    return this.stepper.atOperatingPoint(this.dcOperatingPoint);
  }

  ensureStepSize() {
    // Resolve topology edges finely, use a medium step while threshold timing matters, then continue
    // at a coarse step until the solved DC operating point is actually reached. These horizons select
    // numerical resolution only; they never declare the circuit settled.
    const wanted = this.electricalMs < this.fineUntilMs
      ? 0.00002
      : this.externalToneActive || this.tv20s?.hasDynamics(this.electricalMs) ? 0.0001
        : this.electricalMs < this.mediumUntilMs ? 0.0005
          : 0.010;
    if (wanted !== this.dt) this.rebuild(wanted);
  }

  stepFor(milliseconds, detectInputs = true) {
    const target = this.electricalMs + milliseconds;
    while (this.electricalMs + 1e-9 < target) {
      // Static intervals may be jumped only after the live storage/discrete state agrees with the
      // solver's DC operating point. Media is an explicitly bounded representative waveform: once
      // its medium-resolution exercise is complete, its remaining file duration is policy-only time.
      const boundedMediaComplete = this.mediaActive && this.electricalMs >= this.mediumUntilMs;
      if (!this.externalToneActive && (this.atOperatingPoint() || boundedMediaComplete)) {
        this.electricalSeconds += (target - this.electricalMs) / 1000;
        this.electricalMs = target;
        break;
      }
      this.ensureStepSize();
      const requestedMs = Math.min(this.dt * 1000, target - this.electricalMs);
      const beforeMs = this.electricalMs;
      const beforeSeconds = this.electricalSeconds;
      const seed = this.stepper.extractState();
      let stepMs = requestedMs;
      let solved = false;
      let convergenceError = null;
      // A hard source edit can put the TVS, fuse and two LDOs on the same discontinuous edge. As in
      // SPICE, retry that one physical interval with a smaller timestep. Keep a bounded ladder (and
      // the original strict solver) so a genuinely unsolved topology still fails clearly.
      for (const scale of [1, 0.8, 0.64, 0.5, 0.32, 0.2, 0.1, 0.04, 0.01]) {
        stepMs = requestedMs * scale;
        this.electricalMs = beforeMs;
        this.electricalSeconds = beforeSeconds;
        if (Math.abs(stepMs / 1000 - this.dt) > 1e-12 || scale !== 1)
          this.rebuild(stepMs / 1000, seed);
        this.electricalSeconds = beforeSeconds + stepMs / 1000;
        this.electricalMs = beforeMs + stepMs;
        try {
          this.stepper.step(this.electricalSeconds);
          solved = true;
          break;
        } catch (error) {
          if (!/nonlinear solve did not converge/.test(error.message)) throw error;
          convergenceError = error;
        }
      }
      if (!solved) {
        this.electricalMs = beforeMs;
        this.electricalSeconds = beforeSeconds;
        this.rebuild(requestedMs / 1000, seed);
        throw convergenceError;
      }
      this.recordElectrical(false);
      if (this.tv20s) {
        const timedTopologyChanged = this.tv20s.syncTime(this.electricalMs);
        const observedTopologyChanged = this.tv20s.observe({
          nowMs: this.electricalMs,
          voltage: (netName) => this.voltage(netName),
        });
        if (timedTopologyChanged || observedTopologyChanged) {
          const carried = this.stepper.extractState();
          this.invalidateOperatingPoint();
          this.rebuild(this.dt, carried);
          this.stepper.step(this.electricalSeconds);
          this.recordElectrical(false);
        }
      }
      this.recordSample();
      if (detectInputs) {
        const { mask } = this.readInputs(false);
        if (this.lastInputMask !== null && mask !== this.lastInputMask) {
          this.lastInputMask = mask;
          return Math.ceil(this.electricalMs - 1e-9);
        }
        this.lastInputMask = mask;
      }
    }
    return null;
  }

  recordSample() {
    if (this.onSample == null || this.stepper == null) return;
    // Per-electrical-step callbacks exist for safety checks. Current-flow extraction is much more
    // expensive and only belongs in the UI-rate snapshots emitted at firmware/pacing boundaries.
    this.onSample(this.snapshot(false));
  }

  snapshot(detailed = true) {
    const voltages = { [this.stepper.gnd]: 0 };
    for (const net of this.stepper.nodes) voltages[net] = this.stepper.vn[this.stepper.ni[net]];
    const state = this.stepper.extractState();
    return {
      at: this.electricalMs,
      voltages,
      floating: this.stepper.floatingMap(),
      relays: state.relays,
      ssrs: state.ssrs,
      fuses: state.fuses,
      injections: detailed ? this.stepper.padInjections() : [],
      environment: this.tv20s?.snapshot(this.electricalMs) || { mode: 'lab' },
    };
  }

  configureCircuit({ sources, elements, switches }) {
    if (this.tv20s) {
      const unsupportedSources = sources.filter((item) => !item.off && item.net !== '/VBUS');
      if (unsupportedSources.length || elements.length)
        throw new Error('TV20/S mode owns P1-P5; switch to lab mode for manual sources or extra elements');
      const vbus = sources.find((item) => item.net === '/VBUS' && !item.off);
      if (vbus) this.sources.VBUS = source(Number(vbus.v1));
      this.switches = { ...this.switches, ...switches };
      this.invalidateOperatingPoint();
      this.rebuild(0.00002);
      this.recordSample();
      return;
    }
    this.interactiveSources = sources.map((item) => ({ ...item }));
    this.interactiveExtra = elements.map((item) => ({ ...item }));
    this.switches = { ...this.switches, ...switches };
    const dynamic = this.interactiveSources.filter((item) => !item.off && item.type !== 'dc');
    this.externalToneActive = dynamic.length !== 0;
    this.externalStepSeconds = dynamic.length
      ? Math.min(0.00025, ...dynamic.map((item) => item.freq > 0 ? 1 / (Number(item.freq) * 8) : 0.00025))
      : 0.00025;
    this.invalidateOperatingPoint();
    this.rebuild(0.00002);
    this.fineUntilMs = Math.max(this.fineUntilMs, this.nowMs + 8);
    this.mediumUntilMs = Math.max(this.mediumUntilMs, this.nowMs + 100);
    this.recordSample();
  }

  voltage(netName) {
    if (netName === this.stepper.gnd) return 0;
    const index = this.stepper.ni[netName];
    return index === undefined ? Number.NaN : this.stepper.vn[index];
  }

  digital(netName, fallback, strict) {
    const volts = this.voltage(netName);
    if (volts <= 0.825) {
      delete this.indeterminateSince[netName];
      return false;
    }
    if (volts >= 2.475) {
      delete this.indeterminateSince[netName];
      return true;
    }
    if (fallback !== undefined) {
      if (!strict) return fallback;
      const since = this.indeterminateSince[netName] ?? this.nowMs;
      this.indeterminateSince[netName] = since;
      if (this.nowMs - since < 20) return fallback;
    }
    throw new Error(`${netName} is in the ESP32 indeterminate region at ${volts.toFixed(3)} V`);
  }

  readInputs(strict = true) {
    let mask = 0;
    const before = this.lastInputMask ?? 0x0F;
    if (this.digital('/P4_SENSE_N', (before & 0x01) !== 0, strict)) mask |= 0x01;
    if (this.digital('/P5_SENSE_N', (before & 0x02) !== 0, strict)) mask |= 0x02;
    if (this.digital('/K5_SENSE_N', (before & 0x04) !== 0, strict)) mask |= 0x04;
    if (this.digital('/PTT_SENSE_N', (before & 0x08) !== 0, strict)) mask |= 0x08;
    const adcMv = Math.max(0, Math.round(this.voltage('/VBUS_F_ADC') * 1000));
    return { mask, adcMv };
  }

  setOutput(signal, value, at = this.nowMs) {
    if (!(signal in this.outputs)) throw new Error(`unknown firmware output ${signal}`);
    if (this.outputs[signal] === value) return;
    this.outputs[signal] = value;
    this.invalidateOperatingPoint();
    if (signal !== 'DOOR_DRV')
      this.fineUntilMs = Math.max(this.fineUntilMs, Number(at) + 2);
    this.mediumUntilMs = Math.max(this.mediumUntilMs, Number(at) + (signal === 'DOOR_DRV' ? 60 : 30));
  }

  setMedia(active, at = this.nowMs) {
    if (this.mediaActive === active) return;
    this.mediaActive = active;
    this.invalidateOperatingPoint();
    this.fineUntilMs = Math.max(this.fineUntilMs, Number(at) + 5);
    // Exercise the bounded codec tone for longer than the apartment-ring qualification interval;
    // once its masked behavior is established, long file duration is policy-only time.
    this.mediumUntilMs = Math.max(this.mediumUntilMs, Number(at) + (active ? 160 : 20));
  }

  applyEvent(event) {
    if (event.type === 'environment') {
      if (!this.tv20s) throw new Error('TV20/S events require the tv20s environment');
      this.tv20s.apply(event.action, event.at);
      this.tv20s.syncTime(event.at);
      this.invalidateOperatingPoint();
      this.rebuild(0.00002);
      this.fineUntilMs = Math.max(this.fineUntilMs, event.at + 8);
    } else if (event.type === 'source') {
      if (this.tv20s) throw new Error('manual source events require the lab environment');
      this.sources[event.line] = source(event.value);
      this.refreshExternalWave();
      this.invalidateOperatingPoint();
      this.rebuild(0.00002);
      this.fineUntilMs = Math.max(this.fineUntilMs, event.at + 8);
      this.mediumUntilMs = Math.max(this.mediumUntilMs, event.at + 100);
    } else if (event.type === 'tone') {
      this.sources[event.line] = {
        kind: 'tone',
        offset: event.offset ?? 0,
        amplitude: event.amplitude,
        frequency: event.frequency,
      };
      this.refreshExternalWave();
      this.invalidateOperatingPoint();
      this.rebuild(0.00002);
    } else if (event.type === 'pulse') {
      if (!(event.periodMs > 0 && event.widthMs > 0 && event.widthMs < event.periodMs))
        throw new Error('pulse stimulus requires 0 < widthMs < periodMs');
      this.sources[event.line] = {
        kind: 'pulse',
        low: event.low ?? 0,
        high: event.high,
        periodMs: event.periodMs,
        widthMs: event.widthMs,
        delayMs: event.delayMs ?? 0,
        count: event.count ?? null,
        startedSeconds: this.electricalSeconds,
      };
      this.refreshExternalWave();
      this.invalidateOperatingPoint();
      this.rebuild(0.00002);
    } else if (event.type === 'captured') {
      if (!(event.dtMs > 0) || !Array.isArray(event.values) || event.values.length < 2)
        throw new Error('captured stimulus requires dtMs > 0 and at least two values');
      this.sources[event.line] = {
        kind: 'captured',
        dtMs: event.dtMs,
        values: event.values,
        startedSeconds: this.electricalSeconds,
      };
      this.refreshExternalWave();
      this.invalidateOperatingPoint();
      this.rebuild(0.00002);
    } else if (event.type === 'switch') {
      this.switches[event.ref] = event.closed;
      this.invalidateOperatingPoint();
      this.rebuild(0.00002);
      this.fineUntilMs = Math.max(this.fineUntilMs, event.at + 8);
      this.mediumUntilMs = Math.max(this.mediumUntilMs, event.at + 100);
    }
    const timelineEvent = event.type === 'captured'
      ? { ...event, values: `${event.values.length} samples` }
      : { ...event };
    this.timeline.push({ at: event.at, type: 'stimulus', event: timelineEvent });
  }

  recordElectrical(force) {
    const state = this.stepper.extractState();
    const current = {};
    for (const netName of IMPORTANT_NETS) current[netName] = this.voltage(netName);
    for (const [ref, value] of Object.entries(state.relays)) current[ref] = value;
    for (const [ref, value] of Object.entries(state.ssrs)) current[ref] = value;
    for (const [key, value] of Object.entries(current)) {
      const before = this.lastElectrical[key];
      const changed = typeof value === 'boolean' ? before !== value : before === undefined || Math.abs(before - value) > 0.5;
      // The stimulus entry plus raw GPIO transitions describe audio-rate activity compactly; do not
      // expand every captured-tone sample into tens of thousands of analog timeline rows.
      const suppressToneSample = this.externalToneActive && typeof value === 'number' && !force;
      if ((force || changed) && !suppressToneSample)
        this.timeline.push({ at: Math.ceil(this.electricalMs), type: 'electrical', name: key,
          value: typeof value === 'number' ? Number(value.toFixed(3)) : value });
    }
    this.lastElectrical = current;
  }

  advanceTo(targetMs) {
    const target = Number(targetMs);
    if (target < this.nowMs) throw new Error(`time moved backwards: ${target} < ${this.nowMs}`);
    const environmentBoundary = this.tv20s?.nextEventAt(this.electricalMs, target) ?? null;
    const electricalTarget = environmentBoundary == null ? target : Math.min(target, environmentBoundary);
    const crossing = this.stepFor(electricalTarget - this.electricalMs, true);
    if (crossing !== null && crossing <= electricalTarget) {
      // Multiple audio-rate GPIO crossings may occur inside one integer millisecond. Returning the
      // same protocol timestamp is valid because electrical state has advanced; artificially adding
      // 1 ms per crossing would let virtual time outrun the circuit and skip external events.
      this.nowMs = Math.max(this.nowMs, crossing);
      return { at: this.nowMs, reason: 'input' };
    }
    this.nowMs = electricalTarget;
    if (environmentBoundary != null && electricalTarget === environmentBoundary)
      return { at: electricalTarget, reason: 'environment' };
    return { at: electricalTarget, reason: 'deadline' };
  }

  crash(settleMs = 100) {
    this.programPresent = false;
    this.mediaActive = false;
    if (this.interactiveSources !== null)
      this.externalToneActive = this.interactiveSources.some((item) => !item.off && item.type !== 'dc');
    else
      this.refreshExternalWave();
    this.fineUntilMs = Math.max(this.fineUntilMs, this.nowMs + 2);
    this.mediumUntilMs = Math.max(this.mediumUntilMs, this.nowMs + 20);
    this.invalidateOperatingPoint();
    this.rebuild(0.00002);
    if (settleMs > 0) this.stepFor(settleMs, false);
    else this.stepper.step(this.electricalSeconds);
    this.recordElectrical(true);
    this.recordSample();
  }

  rebootProgram() {
    this.programPresent = true;
    this.outputs = { PTT_DRV: false, DOOR_DRV: false, MUTE_DRV: false, P4_ISO: false };
    this.mediaActive = false;
    this.invalidateOperatingPoint();
    this.rebuild(0.00002);
    this.fineUntilMs = Math.max(this.fineUntilMs, this.nowMs + 2);
    this.mediumUntilMs = Math.max(this.mediumUntilMs, this.nowMs + 20);
    this.recordSample();
  }
}

export class FirmwareCircuitRunner extends EventEmitter {
  constructor({ socketPath, startMs = 0, events = [], slowdownMs = 0,
    responseVersion = PROTOCOL_VERSION, interactive = false, fixtureOptions = {} } = {}) {
    super();
    this.socketPath = socketPath;
    this.events = [...events].sort((a, b) => a.at - b.at);
    this.slowdownMs = slowdownMs;
    this.responseVersion = responseVersion;
    this.interactive = interactive;
    this.timeline = [];
    this.fixture = new HeadCircuitFixture({ startMs, timeline: this.timeline, ...fixtureOptions });
    this.pendingCommands = [];
    this.pendingAdvance = null;
    this.horizonMs = Number(startMs);
    this.paused = interactive;
    this.pendingCircuitConfig = null;
    this.pendingEnvironmentActions = [];
    this.failure = null;
    this.connected = false;
  }

  async listen() {
    this.server = net.createServer((socket) => this.accept(socket));
    await new Promise((resolve, reject) => {
      this.server.once('error', reject);
      this.server.listen(this.socketPath, resolve);
    });
  }

  accept(socket) {
    if (this.connected) {
      socket.destroy(new Error('only one firmware process may connect'));
      return;
    }
    this.connected = true;
    this.socket = socket;
    socket.setEncoding('utf8');
    let buffer = '';
    socket.on('data', (chunk) => {
      buffer += chunk;
      while (buffer.includes('\n')) {
        const index = buffer.indexOf('\n');
        const line = buffer.slice(0, index);
        buffer = buffer.slice(index + 1);
        this.handleLine(line).catch((error) => this.fail(error));
      }
    });
    socket.on('close', () => {
      this.connected = false;
      this.socket = null;
      this.pendingAdvance = null;
      this.emit('disconnect');
    });
    socket.on('error', (error) => this.fail(error));
  }

  fail(error) {
    if (this.failure) return;
    this.failure = error instanceof Error ? error : new Error(String(error));
    this.socket?.destroy();
    this.emit('failure', this.failure);
  }

  parseVersion(tokens) {
    if (Number(tokens[1]) !== PROTOCOL_VERSION)
      throw new Error(`protocol version mismatch: expected ${PROTOCOL_VERSION}, got ${tokens[1]}`);
  }

  processEventsThrough(at) {
    while (this.events.length && this.events[0].at <= at) {
      const event = this.events.shift();
      if (event.type === 'command') {
        this.pendingCommands.push(event.command);
        this.timeline.push({ at: event.at, type: 'command', command: event.command });
      } else {
        this.fixture.applyEvent(event);
      }
    }
  }

  nextEventAt(deadline) {
    return this.events.length && this.events[0].at <= deadline ? this.events[0].at : deadline;
  }

  sendAt(reason) {
    const { mask, adcMv } = this.fixture.readInputs();
    const commands = this.pendingCommands.splice(0);
    if (reason === 'boot' || reason === 'external' || commands.length ||
        (reason === 'input' && !this.fixture.externalToneActive))
      this.timeline.push({ at: Math.trunc(this.fixture.nowMs), type: 'at', reason, mask, adcMv });
    const suffix = commands.length ? ` ${commands.join(' ')}` : '';
    this.socket.write(`AT ${this.responseVersion} ${Math.trunc(this.fixture.nowMs)} ${mask} ${adcMv} ${reason} ${commands.length}${suffix}\n`);
    this.emit('update', { reason, at: this.fixture.nowMs });
  }

  setHorizon(targetMs) {
    if (!this.interactive) throw new Error('setHorizon is only available in interactive mode');
    this.horizonMs = Math.max(this.horizonMs, Math.trunc(Number(targetMs)));
    if (this.horizonMs > this.fixture.nowMs) {
      this.applyPendingCircuitConfig();
      this.applyPendingEnvironmentActions();
    }
    this.drainInteractive();
  }

  setPaused(paused) {
    if (!this.interactive) throw new Error('setPaused is only available in interactive mode');
    this.paused = Boolean(paused);
    if (this.paused) {
      // Revoke pacing time granted but not yet consumed. A circuit edit must not let firmware spend
      // stale pacing credit while the UI says paused.
      this.horizonMs = this.fixture.nowMs;
    }
  }

  pauseAtCurrentTime() {
    this.setPaused(true);
  }

  queueCommand(command) {
    if (!this.interactive) throw new Error('queueCommand is only available in interactive mode');
    this.pendingCommands.push(command);
    this.timeline.push({ at: Math.trunc(this.fixture.nowMs), type: 'command', command });
    if (!this.paused && this.pendingAdvance && this.socket) {
      this.pendingAdvance = null;
      this.sendAt('external');
    }
  }

  queueEnvironmentAction(action) {
    if (!this.interactive) throw new Error('queueEnvironmentAction is only available in interactive mode');
    if (!this.fixture.tv20s) throw new Error('TV20/S actions require the tv20s environment');
    this.pendingEnvironmentActions.push(action);
    this.emit('update', { reason: 'environment-pending', at: this.fixture.nowMs });
    if (!this.paused && this.pendingAdvance && this.socket) {
      this.applyPendingEnvironmentActions();
      this.pendingAdvance = null;
      this.sendAt('external');
    }
  }

  applyPendingEnvironmentActions() {
    if (!this.pendingEnvironmentActions.length) return false;
    const actions = this.pendingEnvironmentActions.splice(0);
    for (const action of actions)
      this.fixture.applyEvent({ type: 'environment', action, at: this.fixture.nowMs });
    this.emit('update', { reason: 'environment', at: this.fixture.nowMs });
    return true;
  }

  cloneCircuitConfig(config) {
    return {
      sources: config.sources.map((item) => ({ ...item })),
      elements: config.elements.map((item) => ({ ...item })),
      switches: { ...config.switches },
    };
  }

  applyCircuitConfig(config) {
    this.fixture.configureCircuit(config);
    this.emit('update', { reason: 'circuit', at: this.fixture.nowMs });
    if (this.interactive && !this.paused && this.pendingAdvance && this.socket) {
      this.pendingAdvance = null;
      this.sendAt('external');
    }
  }

  applyPendingCircuitConfig() {
    if (this.pendingCircuitConfig == null) return false;
    const config = this.pendingCircuitConfig;
    this.pendingCircuitConfig = null;
    this.applyCircuitConfig(config);
    return true;
  }

  configureCircuit(config, { immediate = false } = {}) {
    if (this.interactive && this.paused && !immediate) {
      // Paused freezes the complete circuit snapshot, not merely integration time. Keep source and
      // topology edits as a boundary event until +1 ms or resume grants time. Repeated edits at the
      // same frozen instant collapse to their final configuration.
      this.pendingCircuitConfig = this.cloneCircuitConfig(config);
      this.emit('update', { reason: 'circuit-pending', at: this.fixture.nowMs });
      return;
    }
    this.pendingCircuitConfig = null;
    this.applyCircuitConfig(config);
  }

  drainInteractive() {
    if (!this.interactive || !this.pendingAdvance || !this.socket || this.failure) return;
    const { deadline } = this.pendingAdvance;
    if (this.pendingCommands.length) {
      this.pendingAdvance = null;
      this.sendAt('external');
      return;
    }
    if (this.pendingEnvironmentActions.length && this.horizonMs > this.fixture.nowMs) {
      this.applyPendingEnvironmentActions();
      this.pendingAdvance = null;
      this.sendAt('external');
      return;
    }
    const boundary = Math.min(deadline, this.nextEventAt(deadline), this.horizonMs);
    if (boundary <= this.fixture.nowMs) return;
    const result = this.fixture.advanceTo(boundary);
    this.pendingAdvance = null;
    if (result.reason === 'input') {
      this.sendAt('input');
      return;
    }
    if (result.reason === 'environment') {
      this.sendAt('external');
      return;
    }
    if (this.events.length && this.events[0].at <= boundary) {
      this.processEventsThrough(boundary);
      this.sendAt('external');
    } else if (boundary >= deadline) {
      this.sendAt('deadline');
    } else {
      // The host treats stop reasons as diagnostics. Returning at the pacing horizon lets the
      // browser pause virtual time without changing ESPHome scheduler semantics.
      this.sendAt('pace');
    }
  }

  async handleLine(line) {
    if (this.slowdownMs) await new Promise((resolve) => setTimeout(resolve, this.slowdownMs));
    const tokens = line.trim().split(/\s+/);
    const kind = tokens[0];
    this.parseVersion(tokens);
    if (kind === 'HELLO') {
      if (this.interactive && !this.fixture.programPresent) this.fixture.rebootProgram();
      this.fixture.validateHello(tokens.slice(2));
      this.processEventsThrough(this.fixture.nowMs);
      this.sendAt('boot');
      return;
    }
    if (kind === 'WRITE') {
      const [, , at, sequence, pinText, valueText] = tokens;
      const pin = Number(pinText);
      const signal = GPIO_TO_SIGNAL[pin];
      if (!['PTT_DRV', 'DOOR_DRV', 'MUTE_DRV', 'P4_ISO'].includes(signal))
        throw new Error(`WRITE targets non-output GPIO${pin}`);
      const value = valueText === '1';
      this.fixture.setOutput(signal, value, Number(at));
      this.timeline.push({ at: Number(at), type: 'write', sequence: Number(sequence), signal, value });
      this.emit('update', { reason: 'write', at: Number(at) });
      return;
    }
    if (kind === 'MEDIA') {
      const [, , at, state, name, duration] = tokens;
      this.fixture.setMedia(state === 'START', Number(at));
      this.timeline.push({ at: Number(at), type: 'media', state, name, duration: Number(duration) });
      this.emit('update', { reason: 'media', at: Number(at) });
      return;
    }
    if (kind === 'EMIT') {
      const [, , at, name, value] = tokens;
      this.timeline.push({ at: Number(at), type: 'entity', name, value: value === '1' });
      this.emit('update', { reason: 'entity', at: Number(at) });
      return;
    }
    if (kind === 'ADVANCE') {
      const now = Number(tokens[2]);
      const deadline = Number(tokens[3]);
      if (now !== this.fixture.nowMs)
        throw new Error(`ADVANCE now mismatch: host=${now}, runner=${this.fixture.nowMs}`);
      if (this.interactive) {
        if (this.pendingAdvance) throw new Error('host sent ADVANCE while one was already pending');
        this.pendingAdvance = { now, deadline };
        this.drainInteractive();
        return;
      }
      const boundary = this.nextEventAt(deadline);
      const result = this.fixture.advanceTo(boundary);
      if (result.reason === 'input') {
        this.sendAt('input');
        return;
      }
      if (result.reason === 'environment') {
        this.sendAt('external');
        return;
      }
      if (boundary < deadline || (this.events.length && this.events[0].at === boundary)) {
        this.processEventsThrough(boundary);
        this.sendAt('external');
      } else {
        this.sendAt('deadline');
      }
      return;
    }
    throw new Error(`unknown host message ${kind}`);
  }

  async close() {
    this.socket?.destroy();
    if (this.server) await new Promise((resolve) => this.server.close(resolve));
  }

  compactTimeline() {
    return this.timeline.map((item) => JSON.stringify(item)).join('\n');
  }
}
