gunnarbeutner/doorbell/sim/src/components/index.js

// Component registry: classify a raw component to its class, and assemble simulation elements.
import { simulate, gndOf } from '../engine.js';
import { ParameterOverrides } from '../parameters.js';

import EsdArray from './EsdArray.js';
import Relay from './Relay.js';
import SolderBridge from './SolderBridge.js';
import Switch from './Switch.js';
import Transformer from './Transformer.js';
import Photomos from './Photomos.js';
import Optocoupler from './Optocoupler.js';
import Ldo from './Ldo.js';
import Ic from './Ic.js';
import Mosfet from './Mosfet.js';
import DiodeArray from './DiodeArray.js';
import Diode from './Diode.js';
import FerriteBead from './FerriteBead.js';
import Inductor from './Inductor.js';
import Capacitor from './Capacitor.js';
import Speaker from './Speaker.js';
import Fuse from './Fuse.js';
import Resistor from './Resistor.js';
import TestPoint from './TestPoint.js';
import Connector from './Connector.js';
import Unmodeled from './Unmodeled.js';

// most-specific first; the first class whose compatible() matches wins
export const REGISTRY = [
  EsdArray,
  Relay,
  SolderBridge,
  Switch,
  Transformer,
  Photomos,
  Optocoupler,
  Ldo,
  Ic,
  Mosfet,
  DiodeArray,
  Diode,
  FerriteBead,
  Inductor,
  Capacitor,
  Speaker,
  Fuse,
  Resistor,
  TestPoint,
  Connector,
];

export function classify(comp) {
  const Cls = REGISTRY.find((C) => C.compatible(comp)) || Unmodeled;
  return new Cls(comp);
}

export function allComponents(netlist) {
  return netlist.components.map(classify);
}

// switch state at power-up: solder bridges start closed, everything else open
export function defaultSwitchState(netlist) {
  const ss = {};

  for (const c of allComponents(netlist)) {
    if (c.defaultClosed) ss[c.ref] = true;
  }

  return ss;
}

// every simulation element: each part's model + any hand-added extras. `program` lets a test set the
// behavioural state of the modelled ICs (e.g. { U1: { '/PTT_DRV': vf }, U3: { out: vf } }) so their
// drivers are emitted from inside the part — the test then injects only the real rails (VBUS/GND/bus).
// `omit` drops a component's elements entirely (fault injection: a dead part whose pins all dangle,
// e.g. a failed-open SSR) — the netlist itself stays untouched.
export function buildElements(netlist, { switchState = {}, extra = [], program = {}, omit = [], params = {} } = {}) {
  const els = [];
  const skip = new Set(omit);
  const components = allComponents(netlist);
  const resolved = new ParameterOverrides(params, components.map((c) => c.ref));

  for (const c of components) {
    if (skip.has(c.ref)) continue;
    for (const e of c.elements({ switchState, program, params: resolved })) els.push(e);
  }

  for (const e of extra) els.push(e);

  resolved.assertConsumed();
  els.resolvedParams = resolved.snapshot();

  return els;
}

// high-level scenario for tests: drive `sources` ({net: volts | vf(t)}), set `switches`
// ({ref: pressed?}), set IC behavioural state via `program` ({ref: {...}}, e.g. an ESP GPIO driven
// through its real output impedance rather than pinned as an ideal source), inject any hand-built
// `extra` elements (e.g. a surge through a series resistor); returns the final node voltages + floating flags.
export function runDC(netlist, { sources = {}, switches = {}, extra = [], program = {}, omit = [], params = {}, gnd, T = 0.04, dt = 20e-6 } = {}) {
  const switchState = { ...defaultSwitchState(netlist), ...switches };
  const els = buildElements(netlist, { switchState, extra, program, omit, params });

  const srcs = Object.entries(sources).map(([net, v]) => ({
    net,
    vf: typeof v === 'function' ? v : () => v,
  }));

  const r = simulate(els, srcs, gnd || gndOf(netlist), T, dt);

  const V = {};
  for (const n in r.v) V[n] = r.v[n][r.v[n].length - 1];

  return { V, floating: r.floating, RES: r, resolvedParams: els.resolvedParams };
}
